solarlink-ar/solarlink-web/Documentación/Códigos/Carpeta Tecnica Solar Link/Fuentes.tex

\href{https://en.wikipedia.org/wiki/Maximum_power_point_tracking}{Seguidor de punto de maxima potencia, Wikipedia}\\

\href{https://en.wikipedia.org/wiki/Buck_converter}{Conversor buck, Wikipedia}\\

\href{https://es.wikipedia.org/wiki/Controlador_PID}{Controladores PID, Wikipedia}\\

\href{https://oa.upm.es/55985/1/TFG_ALBERTO_JIMENEZ_DE_LA_PENA.pdf}{Diseño de convertidor DC/DC con control reomoto para smartigrids}\\

\href{https://repositorio.uca.edu.ar/bitstream/123456789/11949/1/Bassani%20Mariano.%20TRABAJO%20FINAL%20DE%20MBA_MB_20210311_v2.pdf}{Trabajo final de Facultad de Ciencias Económicas de la UCA: ¿Es negocio invertir en generación eléctrica solar en Argentina?}\\

\href{https://www.un.org/es/chronicle/article/la-promesa-de-la-energia-solar-estrategia-energetica-para-reducir-las-emisiones-de-carbono-en-el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,ahorrar%20600%20kilogramos%20de%20CO2}{Organización de las Naciones Unidas: La promesa de la energía solar: Estrategia energética para reducir las emisiones de carbono en el siglo XXI}\\

\href{https://ri.conicet.gov.ar/handle/11336/182578?show=full}{Estado del arte de la tecnología de celdas solares basadas en semiconductores}\\

\href{https://docs.python.org/3/index.html}{Python 3.12.0 documentation}\\

\href{https://docs.djangoproject.com/en/4.2/}{Django documentation}\\

\href{https://docs.micropython.org/en/latest/}{MicroPython documentation}\\

\href{https://microdot.readthedocs.io/en/latest/}{Microdot documentation}\\

\href{https://github.com/solarlink-ar/solarlink}{Solar Link GitHub}\\

\href{https://solarlink.ar}{Web de Solar Link}\\
