solarlink-ar/solarlink-web/Documentación/Códigos/Presentación Proambiente Solar Link/resumen.tex

Solar Link es un administrador inteligente de energía eléctrica (Smart Grid) único en su tipo, que busca incentivar y maximizar el uso de energías renovables. A través de paneles solares, y con un sistema inteligente, alimentar todo el consumo hogareño posible con energía solar, “switcheando” las líneas de la casa (ejemplo iluminación, tomacorrientes) entre la línea eléctrica del proveedor (edesur o edenor p/ej) y la alimentación renovable.\\

La aplicación web, vinculada con el tablero del usuario, puede mostrar el consumo hogareño en tiempo real, cuánto se consumió de cada origen y se ahorró en el último tiempo, cuánto significa esto en términos de ahorro de dinero en la factura de luz, a modo de concientización en la importancia del uso de este tipo de energía.\\

En caso de cortes de suministro de luz, Solar Link puede encargarse de lo esencial de la casa que haga falta alimentar, siempre que esté en su margen de funcionamiento. \\

Por último, el proyecto plantea ser modular, versátil y económico, de forma tal que el tablero puede trabajar con cualquier cantidad de paneles o baterías que se le suministren: Solar Link no está limitado sólo a una fuente de energía solar. Aunque el enfoque de nuestro proyecto es aprovechar este tipo de energía, el sistema permite aprovechar también cualquier tipo de fuente: desde una red de proveedor extra, pasando por cosas como un grupo electrógeno, y hasta otras fuentes renovables; biogas, eólica, entre otras. \\
