solarlink-ar/solarlink-web/Documentación/Presentación_Proambiente_Solar_Link.pdf

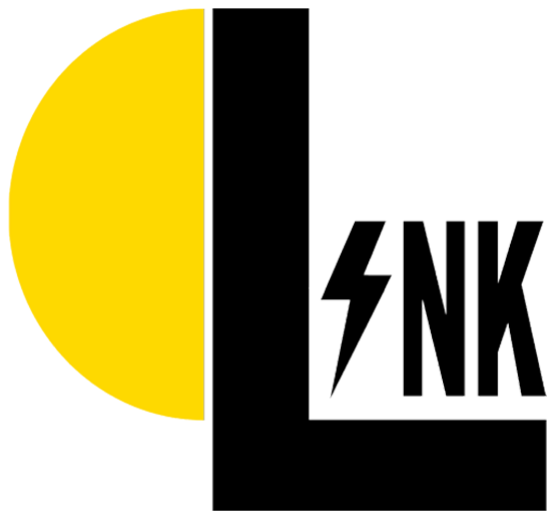
[picture p185: figure]

# Solar Link Propuesta ambiental de futuro sostenible

## Cenyko, Ivan Ezequiel Dias, Lara Paloma Inza Fior, Mateo Palmieri Hise, Agustín Testa, Maximiliano Nicolas

2023

## Índice

1. Preámbulo | 2
2. Resumen del proyecto | 6
3. Desarrollo del proyecto | 6
4. Impacto ambiental | 8
5. Beneficios sociales | 11
6. Conclusiones | 14
7. Anexo | 15

1

## 1. Preámbulo

1.1. ¿Quiénes somos?

Ivan Ezequiel Cenyko


DNI: 46.028.174

Mail: ivancenyko@gmail.com

Linkedin: www.linkedin.com/in/ivan-cenyko/

Programación en microPython y desarrollo web Back-End

Lara Paloma Dias


DNI: 46200006

Mail: palomadias308@gmail.com

Linkedin: www.linkedin.com/in/lara-paloma-dias-598bb9288/

Desarrollo web Front-End

2

Mateo Inza Fior


DNI: 46.579.589

Mail: mateoinzafior@gmail.com

Linkedin: www.linkedin.com/in/mateoinzafior/

Desarrollo web Front-End y programación en microPython

Agustin Palmieri Hise


DNI: 46.364.013

Mail: aguspalmierihise@gmail.com

Linkedin: www.linkedin.com/in/agustin-palmieri-hise/

Diseño y confección eléctrico y electrónico íntegro


Maximiliano Nicolas Testa

DNI: 46.187.213

Mail: maxitesta2012@gmail.com

Linkedin: www.linkedin.com/in/maximiliano-testa/

Programación en C y desarrollo Front-End de la Web-app

3


Figura 1: Equipo Solar Link

### 1.2. Contacto

Podes encontrar a Solar Link en:

Mail: info@solarlink.ar

Pagina Web: www.solarlink.ar

Instagram: www.instagram.com/solarlink.ar/

Github: github.com/solarlink-ar/solarlink

Trello: trello.com/w/2023_721c_solarlink

### 1.3. Docentes a cargo

Sergio Medina
Nos fue de ayuda a la hora de organizar y presentar nuestro proyecto.

4

Fabrizio Carlassara
Nos guió en el desarrollo de todo el software del proyecto.

Diego Palmieri
Nos prestó las herramientas y los medios necesarios para confeccionar el proyecto.

### 1.4. Agradecimientos

Este proyecto no hubiera sido posible sin la colaboracion de los docentes anteriormente mencionados, la Asociación Cooperadora IMPA y las empresas Roverano, Exo y Newton Microscopios.

5

## 2. Resumen del proyecto

Solar Link es un administrador inteligente de energía eléctrica (Smart Grid) único en su tipo, que busca incentivar y maximizar el uso de energías renovables. A través de paneles solares, y con un sistema inteligente, alimentar todo el consumo hogareño posible con energía solar, “switcheando” las líneas de la casa (ejemplo iluminación, tomacorrientes) entre la línea eléctrica del proveedor (edesur o edenor p/ej) y la alimentación renovable.

La aplicación web, vinculada con el tablero del usuario, puede mostrar el consumo hogareño en tiempo real, cuánto se consumió de cada origen y se ahorró en el último tiempo, cuánto significa esto en términos de ahorro de dinero en la factura de luz, a modo de concientización en la importancia del uso de este tipo de energía.

En caso de cortes de suministro de luz, Solar Link puede encargarse de lo esencial de la casa que haga falta alimentar, siempre que esté en su margen de funcionamiento.

Por último, el proyecto plantea ser modular, versátil y económico, de forma tal que el tablero puede trabajar con cualquier cantidad de paneles o baterías que se le suministren: Solar Link no está limitado sólo a una fuente de energía solar. Aunque el enfoque de nuestro proyecto es aprovechar este tipo de energía, el sistema permite aprovechar también cualquier tipo de fuente: desde una red de proveedor extra, pasando por cosas como un grupo electrógeno, y hasta otras fuentes renovables; biogas, eólica, entre otras.

## 3. Desarrollo del proyecto

Nuestra propuesta para solventar algunas desventajas de los sistemas de energía renovable (especialmente la solar) es crear un sistema autónomo e inteligente que, a través de un sistema off-grid, sea capaz de acoplar y desacoplar la casa de la red eléctrica convencional, dependiendo del consumo de la misma.

Este sistema debe ser capaz de leer el consumo de las líneas de la casa, y debe conocer la potencia que el sistema solar instalado puede entregar. De esta manera, cuando se detecte que el consumo de la casa puede ser alimentado por el sistema off-grid, dejará de alimentar la casa con el proveedor

6

de energía eléctrica. Mientras que si el consumo supera el límite establecido, volverá a alimentarla. Para realizar esto, se utiliza la técnica “cruce por cero”, para sincronizar el cambio entre líneas, y que no se note este cambio.

Puede ocurrir que en una casa estén constantemente heladeras, calefactores, computadoras, y otros electrodomésticos de alto consumo en uso, y que el sistema off-grid nunca pueda ser capaz de alimentar la línea general de la casa. Para esto, proponemos que Solar Link trabaje parcialmente sobre la casa, pudiendo alimentar independientemente la línea de iluminación y la línea de tomas de la casa. Es decir, si se da el caso mencionado anteriormente, la línea de iluminación seguiría siendo alimentada por energía solar, mientras que la línea de tomas la sería alimentada por el proveedor de energía eléctrica.

En caso de un corte de suministro de luz,el sistema Solar Link seguiría funcionando, alimentando a la mayor parte de la casa posible.
Un aspecto clave del proyecto es la accesibilidad e interacción con el usuario. Solar Link incluye una aplicación vinculada con sensores distribuidos en la red eléctrica de la casa. El usuario podrá así tener una noción más concreta de cuáles son los principales consumos del hogar, y le brinda la información necesaria a Solar Link para alternar el uso de energía off-grid y energía de red en cada línea modular.

Además, para optimizar la carga del sistema solar, desarrollamos un cargador MPPT de 3 etapas que no solo le da la mejor carga posible a las baterías del sistema, sino que también monitorea el estado de carga de las mismas, y se lo comunica al módulo Solar Link para tenerlo en cuenta a la hora de la conmutación entre lineas, y a la hora de entregarle la mayor cantidad de información posible sobre el sistema al usuario.

7

## 4. Impacto ambiental

### 4.1. El aspecto de energías no renovables

Las principales fuentes de energía con las que cuenta hoy el mundo, petróleo, gas natural y carbón mineral, son de carácter no renovable o convencional; es decir que a medida que se van consumiendo disminuyen sus reservas sin posible reposición, salvo que se descubran nuevos yacimientos.

Este sector de energías convencionales sigue teniendo un papel protagónico en la matriz energética mundial, producto de un mercado con muchos años de desarrollo tecnológico, con un gran capital hundido en infraestructura, costos competitivos y con porcentajes de rendimiento y de potencia firme superiores a las renovables. Sin embargo, el consumo de combustibles de origen fósil tiene un efecto muy negativo para el medio ambiente, ya que el dióxido de carbono que se produce por su combustión es el principal constituyente de lo que se conoce como gases de efecto invernadero, principales responsables del calentamiento global.

Las consecuencias de este efecto son, por ejemplo, el aumento de las temperaturas, los picos de temperaturas extremos, que han venido manifestándose en los últimos años. Es por ello, que las emisiones globales de carbono continúan aumentando, lo que indica la necesidad de un conjunto integral de medidas políticas para lograr la reducción sustancial de las emisiones de carbono.

8


Figura 2: Matriz de generación energética en Argentina

En Argentina, casi el 60 % de la energía producida y distribuida en el país son de carácter no renovable. La visión de Solar Link es aportar a que ésta brecha vaya disminuyendo hasta su exterminacion, volviendo a las energias renovables cabecillas en la generacion de energia.

### 4.2. Uso de baterías en la actualidad

En la actualidad, las baterías de litio están tomando cada vez mas protagonismo en el mercado. Estas, luego de su uso, se vuelven obsoletas y generan desechos que no son reciclables, sin contar que su extracción es altamente nociva y genera residuos contaminantes.

La solución que nosotros proponemos es impulsar el uso de baterías de plomo ácido, que no solo son reciclables hasta en un 80 %, sino que tienen una expectativa de vida mayor. Esto sumado al cargador MPPT de Solar Link, que maximiza el potencial recibido de una fuente de energía renovable y la vida útil de las baterías, creemos que es una solución tanto viable como económica.

9

### 4.3. El aspecto de la energía solar

El sol es el mayor suministro de energía que dispone la humanidad disponible de forma ilimitada y que puede ser aprovechada en cualquier parte del mundo. Existen dos maneras principales de capturar esta energía solar: la fotovoltaica y la térmica, ambas comparten la virtud que pueden ser producidas y consumidas en cualquier lugar, tanto en áreas remotas o grandes ciudades.

En las economías emergentes, como la Argentina, donde existe déficit de infraestructura en generación, transporte y distribución, esta energía permite soluciones de generación a los individuos o poblaciones aisladas.

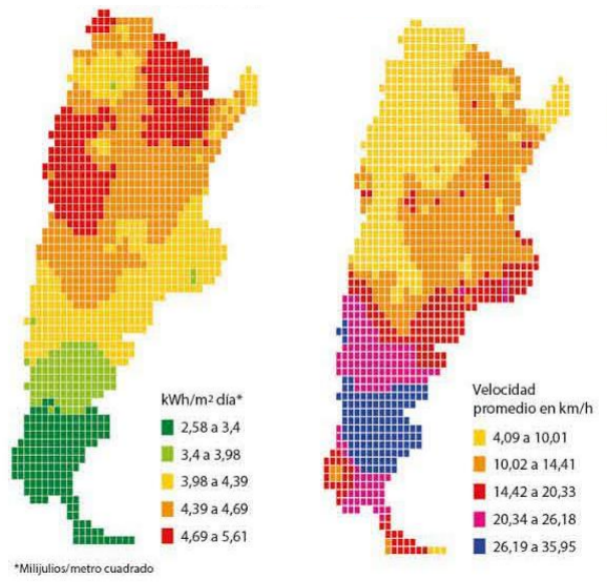
[picture p186: figure]

(a) Zonas del pais con mayor promedio de intensidad de
radiación solar
(b) Zonas del pais con mayor promedio de intensidad de
los vientos

Nótese que justamente las provincias con más potencial solar (inclusive eólico) son aquellas donde el consumo de energía eléctrica es mucho más caro en comparación con el gran Bs As y otros centros urbanos, principalmente por los altos costos de distribución de energía. Acá es donde Solar

10

Link tendría su mayor aprovechamiento.

Considerando la estadística mostrada, un metro cuadrado de panel solar (en bs as) podría generar 4 kW/h por día. Suponiendo que el panel está en uso 12hs por día, se generan 330 W/h por metro cuadrado de panel. En realidad, los paneles son menos eficientes que esto, por tanto para recibir esos 330W/h los paneles son más grandes que 1 metro cuadrado.
Sabiendo esto, usaremos como ejemplo un panel solar de 380 W/h y 1.75 metros cuadrados. Por tanto durante, en promedio, 12 hs, se recibirán 380 W/h en el panel. Esta generación de energía implica que por día se producen 4.56 kW/h.

En promedio, por mes, una casa de núcleo familiar consume 600 kW/h, o sea 20 kW/h por día. Si hacemos números, nos da que el sistema sería capaz de alimentar con energía solar el 25 % de esa carga (en promedio), ya que de los 600 kW/h por mes, 140 pudieron generarse con el sistema para cargar las baterías y que estas después alimenten las líneas competentes.

Hoy en dia el desarrollo de la tecnologia relacionado con la energía solar crece exponencialmente, haciendo mas barato y accesible estos sistemas. A su vez, en argentina disminuye el subsidio destinado a la distribución eléctrica, cerrando lentamente la brecha monetaria entre pagar la luz y recurrir a energias renovables.

Teniendo en cuenta todo lo dicho anteriormente, el uso de energias renovables no solo se esta volviendo plausible, sino que tambien se esta volviendo rentable y accesible. Nuestro objetivo con Solar Link es volver esta esperanza en una realidad.

## 5. Beneficios sociales

### 5.1. Beneficio económico

Solar Link propone el uso de un sistema solar off-grid de baja potencia, el cual es la alternativa mas económica que se consigue de energía solar. Este sistema consta de panel/es solar/es, batería/s, nuestro cargador MPPT de 3 etapas y un inverter.

El sistema que recomendamos instalar en un hogar promedio en Argentina, se compone de dos paneles solares de 380W, un inverter de 2000W,

11 dos baterías de ciclo profundo de 110Ah, el cargador MPPT de 3 etapas de Solar Link, y el módulo Solar Link, con un costo total aproximado de esto ARS $1.600.000 (USD $1.600).

Mientras tanto, un sistema comparable on-grid, puede salir ARS $5.000.000 (USD $5.000). Esto depende del servicio que se contrate y de la empresa que lo realice.

No está de más mencionar que al uno producir la energía que consume, se disminuye el consumo de energía de terceros, el del proveedor eléctrico. Esto quiere decir, que todos los meses se verá reducido el precio que hay que pagar por el suministro de energía eléctrico.

El ahorro en este caso no es lineal. Si uno termina consumiendo a fin de mes la mitad de energía que consumiría normalmente, por como funciona el sistema de cobros de las empresas distribuidoras en Argentina, no pagaría la mitad, sino que bastante menos.

Esto ocurre porque las empresas establecen un precio para cada KW/h dependiendo de la escala en donde se consuma. Por ejemplo, entre 0KW/h y 200KW/h tiene un precio asignado, entre 200KW/h y 400KW/h otro mayor, y si se exceden esos 400KW/h otro inclusive mayor (estas escalas dependen de la empresa a cargo del suministro eléctrico).

Osea, digamos, que cada KW/h entre 0KW/h y 200KW/h valga 1, entre 200KW/h y 400KW/h, 1,5, y si es mayor a 400KW/h, 2. si uno consume 600KW/h, estaría pagando 900, mientras que si uno consume 300KW/h, estaría pagando 350, bastante menos de la mitad. Este ejemplo ilustra como funciona el sistema de cobros de las compañías distribuidoras en Argentina. Las escalas y los valores son a modo de ejemplo. Pueden ser diferentes segun la empresa, la región, y el momento en donde se analice.

### 5.2. Incentivo y concientización

A través de nuestra aplicación, el usuario tendrá acceso a toda la información que respecta al consumo eléctrico de su casa. Esto le permite conocer al detalle no solo el consumo total, sino tambien el consumo que generó el sistema solar propio.

Esto genera en el usuario un sentido de ganancia y de gasto propio. Saber

12 bien cuanto se esta gastando, porque y cuanto de este gasto se amortiguo ayuda a concientizar sobre el consumo de energia en general.

Mas allá del gasto de energía, tener un sistema que, ya sea de manera directa o indirecta, ayuda al medio ambiente, tiene un efecto positivo para la psiquis y para el entorno donde uno vive. Saber que uno esta aportando su grano de arena (siendo el mismo economicamente viable y rentable) genera tranquilidad y un sentido de responsabilidad ciudadana.

### 5.3. Estado del arte

Actualmente, en el mercado argentino, existen principalmente tres tipos de instalaciones de energía solar para un hogar. Cada tipo cuenta con sus propias ventajas y desventajas:

Tipo | Ventajas | Desventajas
On-Grid | Sistema acoplado a la línea doméstica Alimenta casi el 100 % con energía solar | Alto costo Desperdicio de energía
Off-Grid | Económico Acumula energía | Requiere una línea exclusiva para este sistema
Híbrido | Sistema acoplado a la línea doméstica Acumula energía | Potencia limitada Requiere instalación especial

Los sistemas on-grid, como su nombre lo indica, se instalan directamente
en la línea de la casa. Toda la energía que producen los paneles se entregan a la línea general de la casa, sin almacenarse en ningún lado. Si la casa consume mas que lo que generan los paneles, se consume la energía correspondiente a este exceso del proveedor eléctrico, y si consume menos, la energía generada por demás se entrega a la red eléctrica del proveedor.

Para este tipo de sistemas es necesaria la instalación de un medidor bidireccional, que mide tanto el consumo de la casa como lo que devuelve por el exceso en la producción. Si bien este medidor descuenta lo que uno devuelve a la red eléctrica, lo que uno consume es mas caro, no es muy redituable y no su instalación depende del proveedor de energía eléctrica.

Los sistemas off-grid, por otra parte, acumulan la energía generada por los paneles solares en baterías, para luego convertirla en los 220Vac que necesita la casa. El problema de esto, es que la energía extraída de las baterías no se puede incorporar directamente a la línea de la casa, por lo que

13 es necesario la utilización de una línea exclusiva para lo que este sistema genere. Esto implica tener que hacer una instalación eléctrica aislada e independiente del resto de la casa, algo impráctico si además se tiene en cuenta que la utilización de esta línea debe ser controlada y depende directamente de la carga de los paneles.

Los sistemas híbridos son sistemas solares off-grid que se incorporan a la línea de la casa. Pueden utilizar tanto la energía solar acumulada como la energía del proveedor eléctrico. Para utilizar este tipo de sistema es necesaria una instalación especial, que se tiene que realizar en líneas dedicadas. Además, por como es su principio de funcionamiento, el sistema solar no es expandible, por lo que la potencia instalada en un principio no podrá modificarse.

Mientras tanto, Solar Link busca recopilar todas las ventajas de estos 3 tipos de sistemas solares, y dejar en el camino todas las desventajas posibles. Se podría decir que Solar Link es un sistema que acumula y utiliza energía solar, acoplado a la línea de la casa, económico, modular expandible y amigable con el usuario, compartiendo toda la información necesaria sobre el sistema solar instalado y el consumo de la casa.

## 6. Conclusiones

Solar Link aprovecha sus cualidades como gestor inteligente para poder aprovechar la energía solar al máximo. Usualmente, la instalación de una fuente de energía solar por sí sóla no daría abasto para toda la casa (recordemos que en nuestro ejemplo sólo cubría el 30 %), y otros tipos de implementación alternativas a una red inteligente serían rígidas e ineficientes. A través de Solar Link, buscamos que con el control automático de consumo y la separación modular de las redes de la casa logremos maximizar la eficiencia en el consumo, y minimizar los gastos posibles.

Nuestro objetivo es introducir al país un sistema capaz de evitar energía cuya generación es, en su mayoría, resultado de fomentar el cambio climático, introduciendo energías renovables y control y concientización del consumo a sus usuarios, en otras palabras un smart grid con energías renovables. Por otro lado, otorga a sus usuarios energía generada por ellos mismos para su hogar, y por lo tanto, no deben pagar por ella.

Entre sus beneficios están, el uso de energías renovables, la producción de energía en el propio entorno de uso, que reduciría el consumo en la boleta,

14 una aplicación web que permite ver el consumo y configurarlo, dando control al usuario de su consumo y que sea consciente de este.

## 7. Anexo

### 7.1. Referencias

Trabajo final de Facultad de Ciencias Económicas de la UCA: ¿Es negocio invertir en generación eléctrica solar en Argentina? (https://repositorio.uca.edu.ar/bitstream/123456789/11949/1/Bassani%20Mariano.%20TRABAJO%20FINAL%20DE%20MBA_MB_20210311_v2.pdf)

Organización de las Naciones Unidas: La promesa de la energía solar: Estrategia energética para reducir las emisiones de carbono en el siglo XXI (https://www.un.org/es/chronicle/article/la-promesa-de-la-energia-solar-estrategia-energetica-para-reducir-las-emisiones-de-carbono-en-el)

Estado del arte de la tecnología de celdas solares basadas en semiconductores (https://ri.conicet.gov.ar/handle/11336/182578?show=full)

15
