solarlink-ar/solarlink-web/Documentación/Códigos/Carpeta de campo/informes/876842E6-08C9-4F52-9927-B1110389220B.jpg

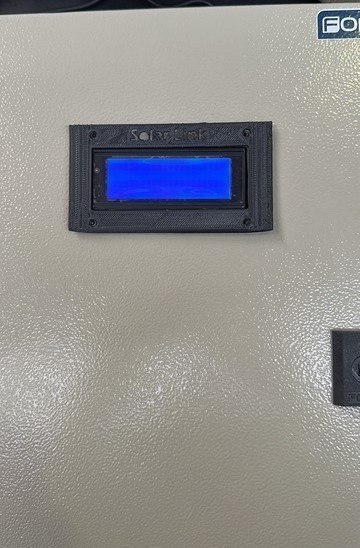
Documentación/Códigos/Carpeta de campo/informes/876842E6-08C9-4F52-9927-B1110389220B.jpg
