solarlink-ar/solarlink-web/Documentación/Códigos/Carpeta de campo/informes/E2ECCB4C-C0EE-4EAA-B4AB-5EC7912F2BAF.jpg

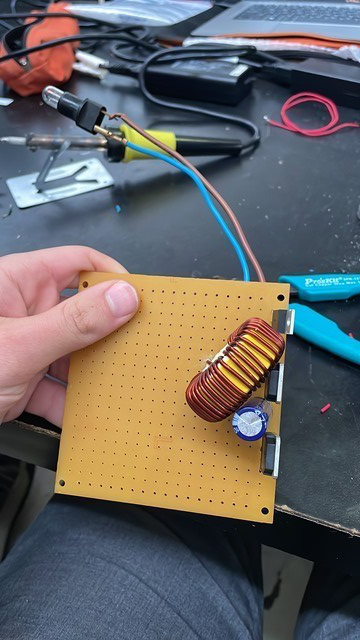
Documentación/Códigos/Carpeta de campo/informes/E2ECCB4C-C0EE-4EAA-B4AB-5EC7912F2BAF.jpg
