solarlink-ar/solarlink-web/Documentación/Códigos/Carpeta de campo/informes/IMG_8020.jpg

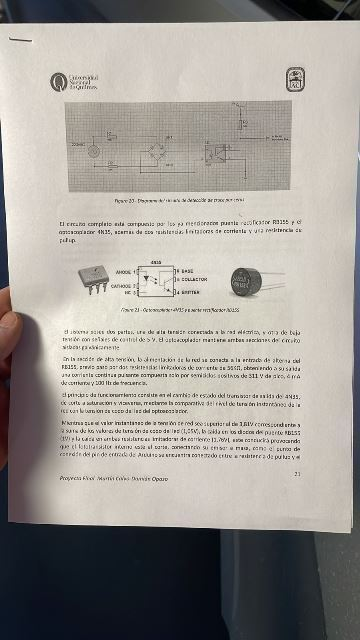
Documentación/Códigos/Carpeta de campo/informes/IMG_8020.jpg
