solarlink-ar/solarlink-web/Documentación/Códigos/Carpeta de campo/informes/IMG_8021.jpg

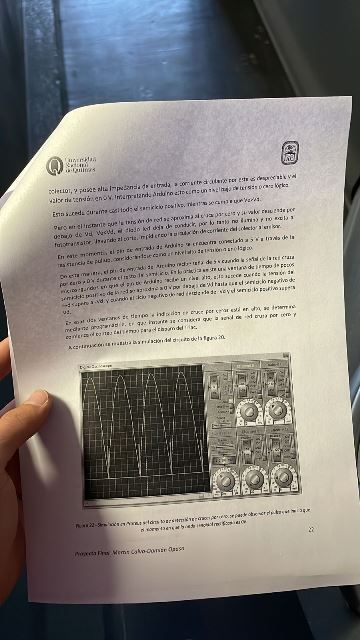
Documentación/Códigos/Carpeta de campo/informes/IMG_8021.jpg
