solarlink-ar/solarlink-web/Documentación/Códigos/Carpeta de campo/informes/IMG_8863.jpg

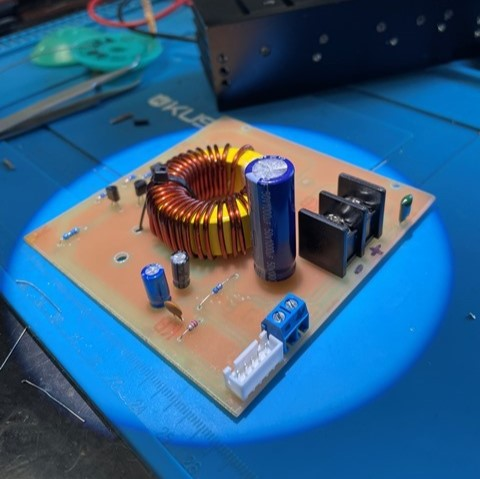
Documentación/Códigos/Carpeta de campo/informes/IMG_8863.jpg
