solarlink-ar/solarlink-web/Documentación/Códigos/Carpeta de campo/informes/IMG_9290.jpg

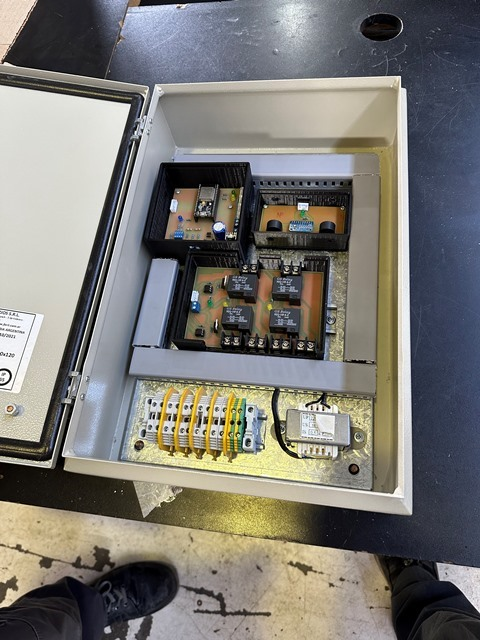
Documentación/Códigos/Carpeta de campo/informes/IMG_9290.jpg
