solarlink-ar/solarlink-web/Documentación/Códigos/Carpeta de campo/informes/IMG_9307.jpg

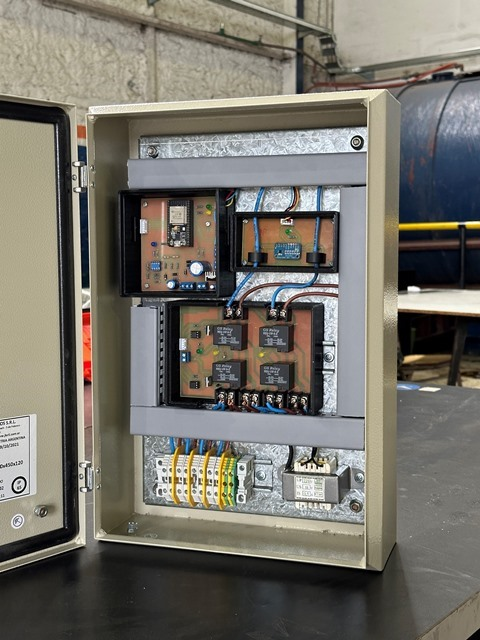
Documentación/Códigos/Carpeta de campo/informes/IMG_9307.jpg
