solarlink-ar/solarlink-web/Documentación/Códigos/Carpeta de campo/informes/Screenshot_5.jpg

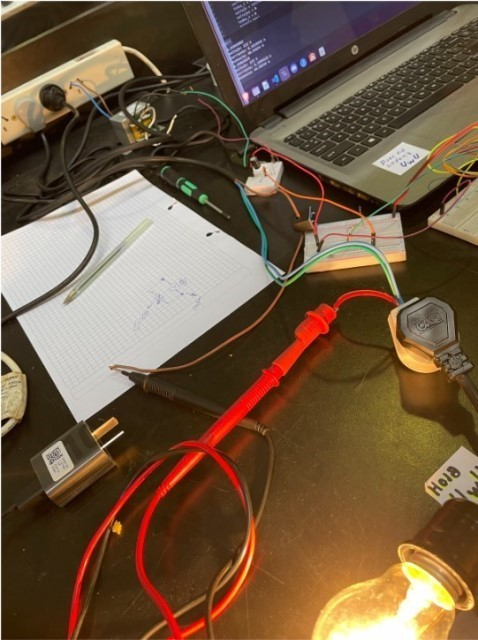
Documentación/Códigos/Carpeta de campo/informes/Screenshot_5.jpg
