solarlink-ar/solarlink-web/Documentación/Códigos/Carpeta de campo/informes/Screenshot_9.jpg

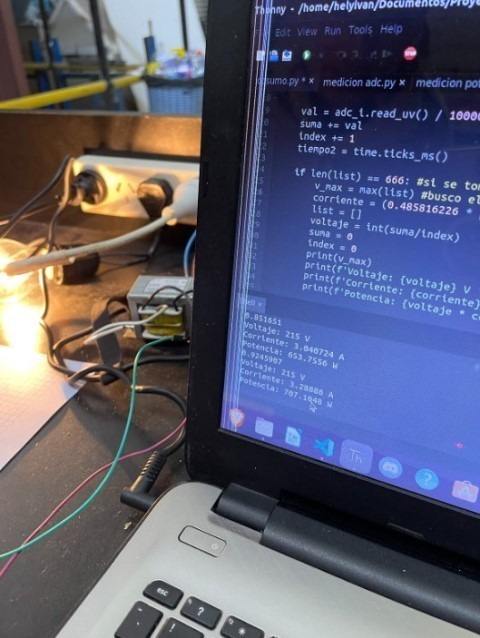
Documentación/Códigos/Carpeta de campo/informes/Screenshot_9.jpg
