solarlink-ar/solarlink-web/Documentación/Códigos/Carpeta Tecnica Solar Link/analisis-tecnico/Diagrama aplicacion SolarLink.png

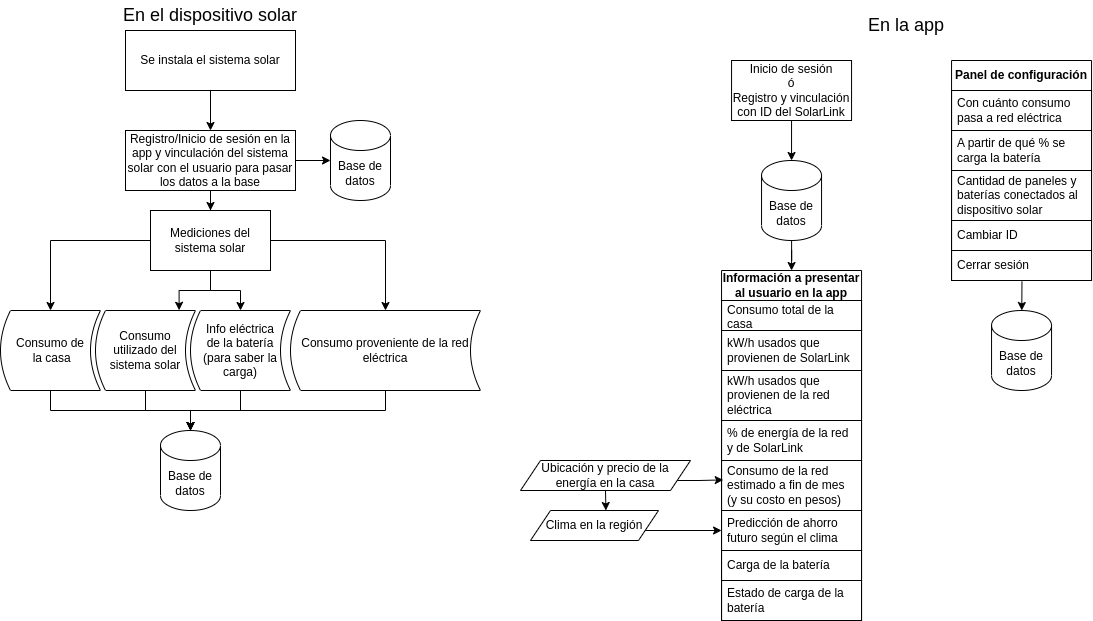
Documentación/Códigos/Carpeta Tecnica Solar Link/analisis-tecnico/Diagrama aplicacion SolarLink.png
