solarlink-ar/solarlink-web/Documentación/Códigos/Carpeta Tecnica Solar Link/hardware/IMG_8938.jpg

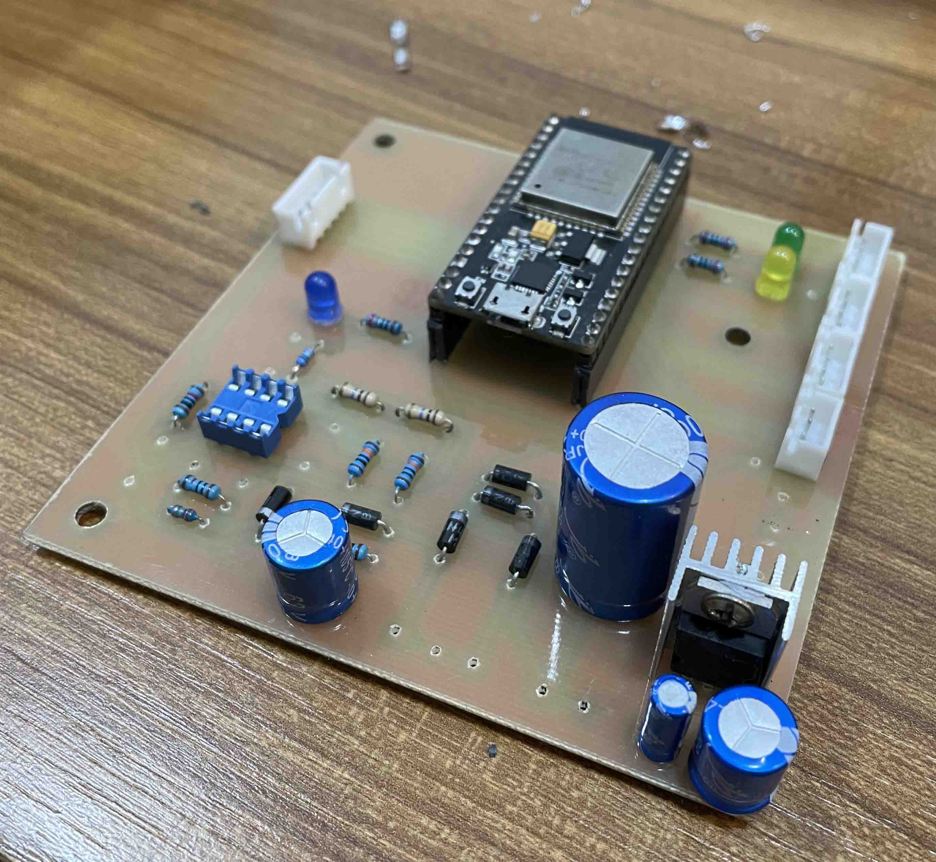
Documentación/Códigos/Carpeta Tecnica Solar Link/hardware/IMG_8938.jpg
