solarlink-ar/solarlink-web/Documentación/Códigos/Carpeta Tecnica Solar Link/hardware/mosfet.jpg

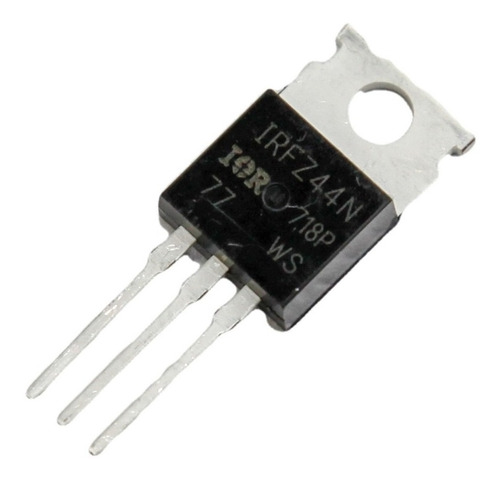
Documentación/Códigos/Carpeta Tecnica Solar Link/hardware/mosfet.jpg
