solarlink-ar/solarlink-web/Documentación/Códigos/Carpeta Tecnica Solar Link/hardware/Screenshot_13.jpg

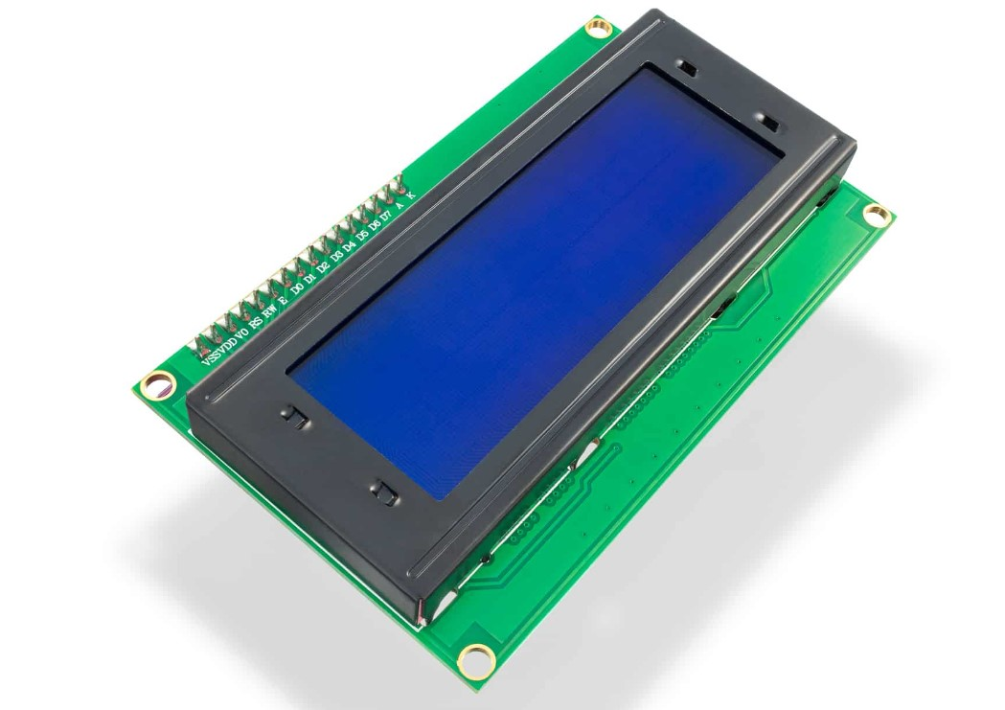
Documentación/Códigos/Carpeta Tecnica Solar Link/hardware/Screenshot_13.jpg
