solarlink-ar/solarlink-web/Documentación/Códigos/Carpeta Tecnica Solar Link/Intro/Screenshot_4.png

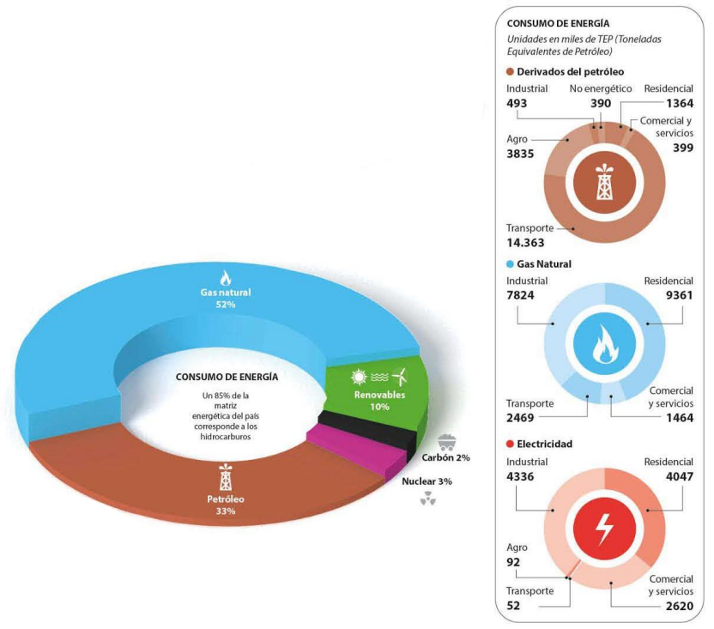
Documentación/Códigos/Carpeta Tecnica Solar Link/Intro/Screenshot_4.png
