solarlink-ar/solarlink-web/Documentación/Códigos/Carpeta Tecnica Solar Link/Intro/smart-grid.png

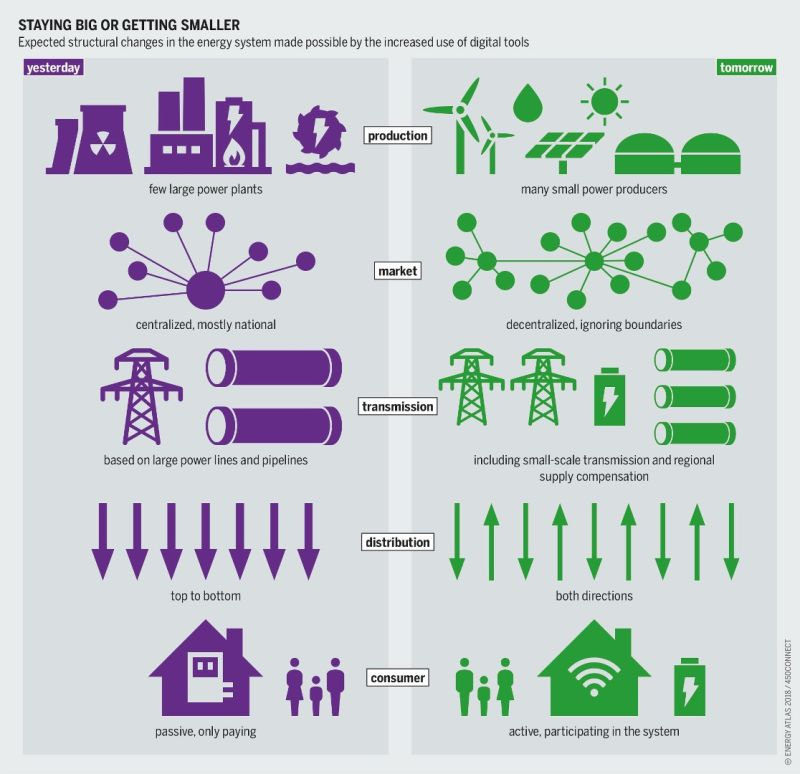
Documentación/Códigos/Carpeta Tecnica Solar Link/Intro/smart-grid.png
