solarlink-ar/solarlink-web/Documentación/Códigos/Carpeta Tecnica Solar Link/MPPT/800px-IUoU_charging_graph.png

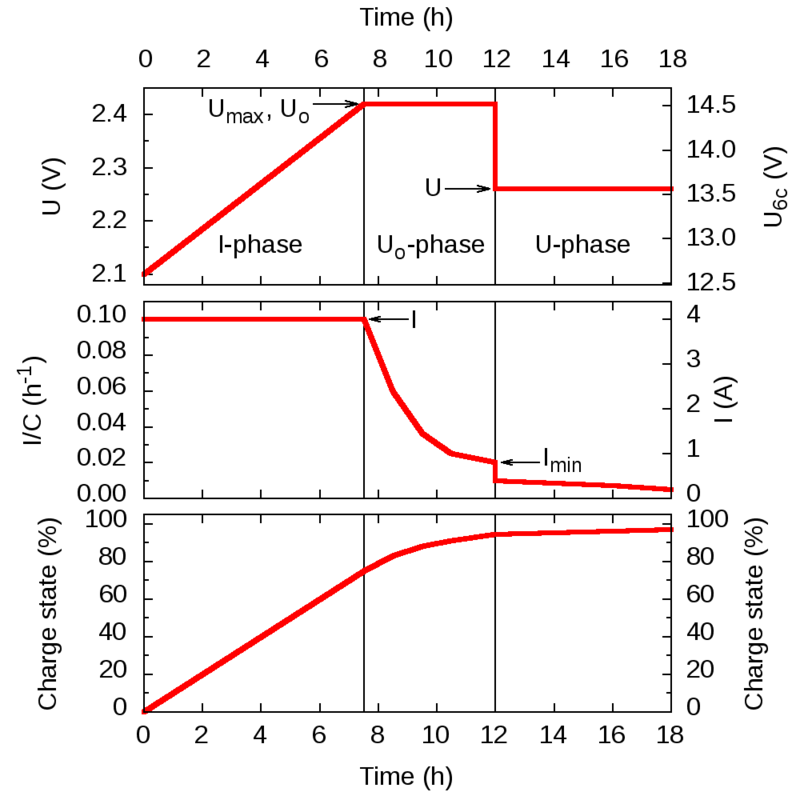
Documentación/Códigos/Carpeta Tecnica Solar Link/MPPT/800px-IUoU_charging_graph.png
