solarlink-ar/solarlink-web/Documentación/Códigos/Carpeta Tecnica Solar Link/MPPT/Screenshot_5.png

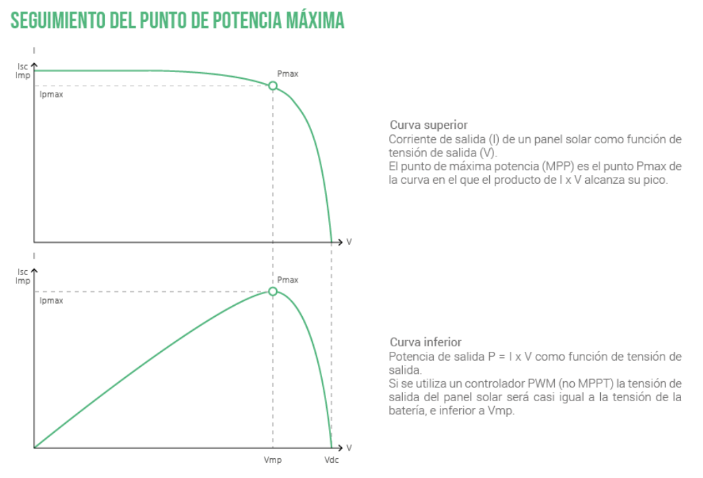
Documentación/Códigos/Carpeta Tecnica Solar Link/MPPT/Screenshot_5.png
