solarlink-ar/solarlink-web/Documentación/Códigos/Carpeta Tecnica Solar Link/MPPT/Screenshot_6.png

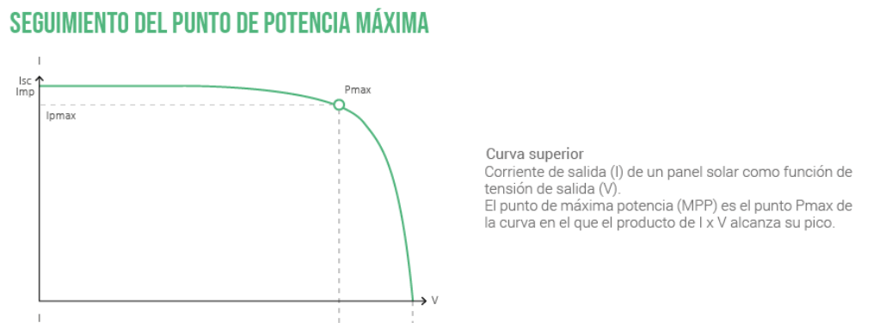
Documentación/Códigos/Carpeta Tecnica Solar Link/MPPT/Screenshot_6.png
