solarlink-ar/solarlink-web/Documentación/Códigos/Carpeta Tecnica Solar Link/preambulo/Captura de pantalla (18).png

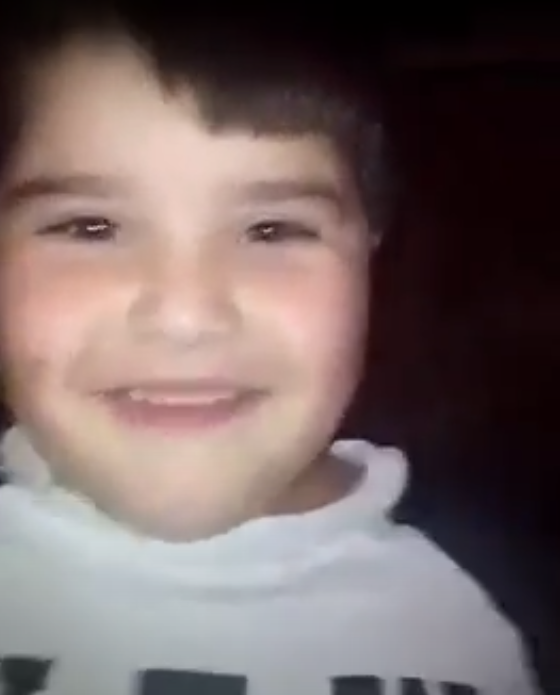
Documentación/Códigos/Carpeta Tecnica Solar Link/preambulo/Captura de pantalla (18).png
