solarlink-ar/solarlink-web/Documentación/Códigos/Carpeta Tecnica Solar Link/proto-final/IMG_7874.jpg

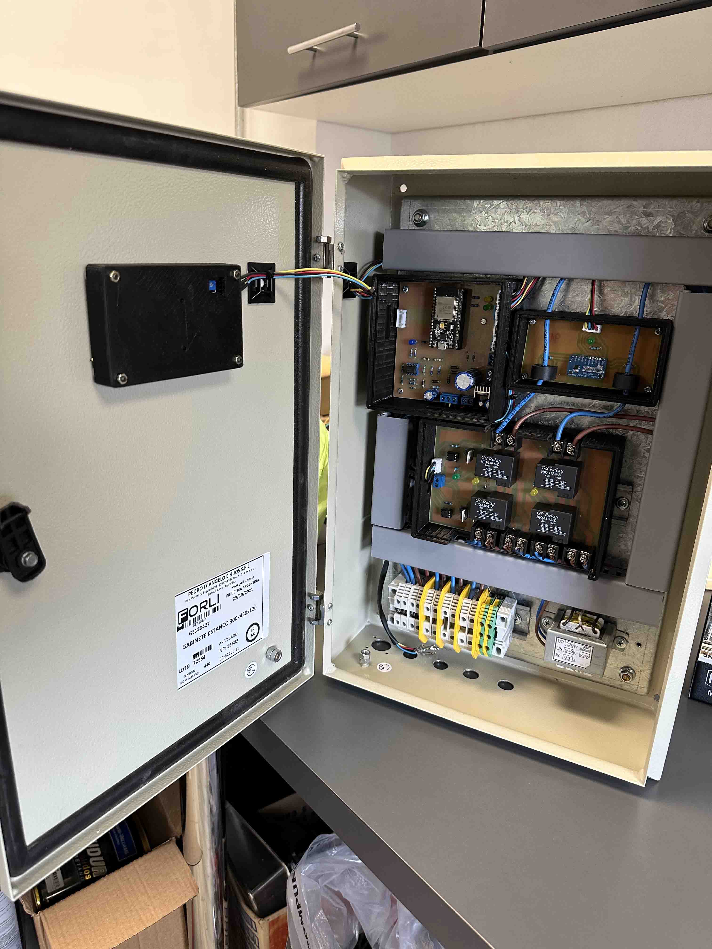
Documentación/Códigos/Carpeta Tecnica Solar Link/proto-final/IMG_7874.jpg
