solarlink-ar/solarlink-web/Documentación/Códigos/Carpeta Tecnica Solar Link/web/Captura desde 2023-10-15 23-22-38.png

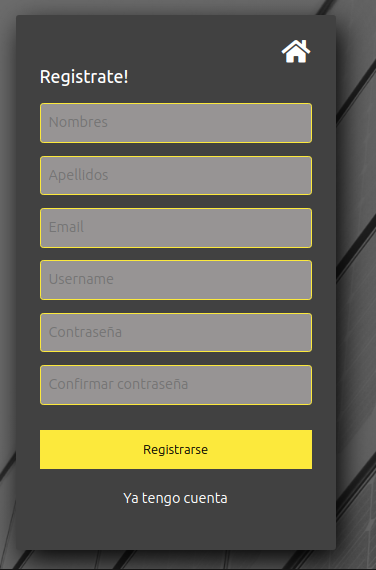
Documentación/Códigos/Carpeta Tecnica Solar Link/web/Captura desde 2023-10-15 23-22-38.png
