solarlink-ar/solarlink-web/PCBs/Conmutación/Screenshot_1.png

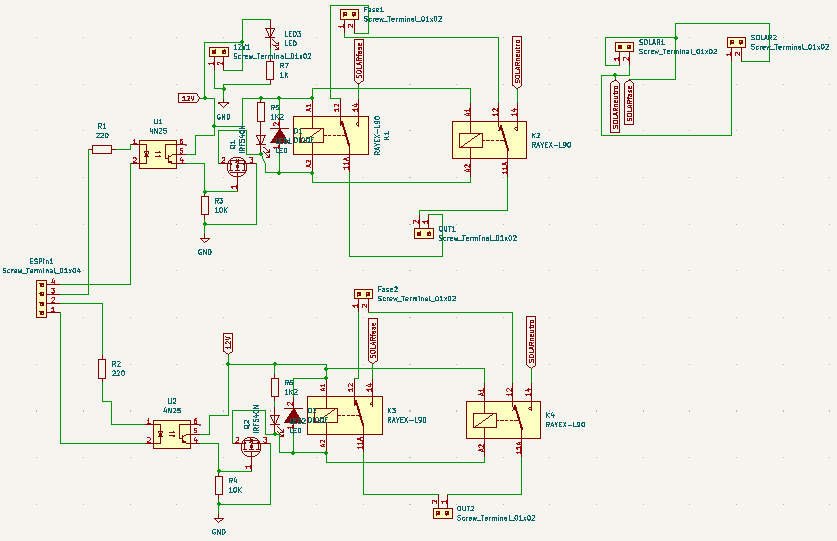
PCBs/Conmutación/Screenshot_1.png
