solarlink-ar/solarlink-web/PCBs/Conmutación/Screenshot_315.png

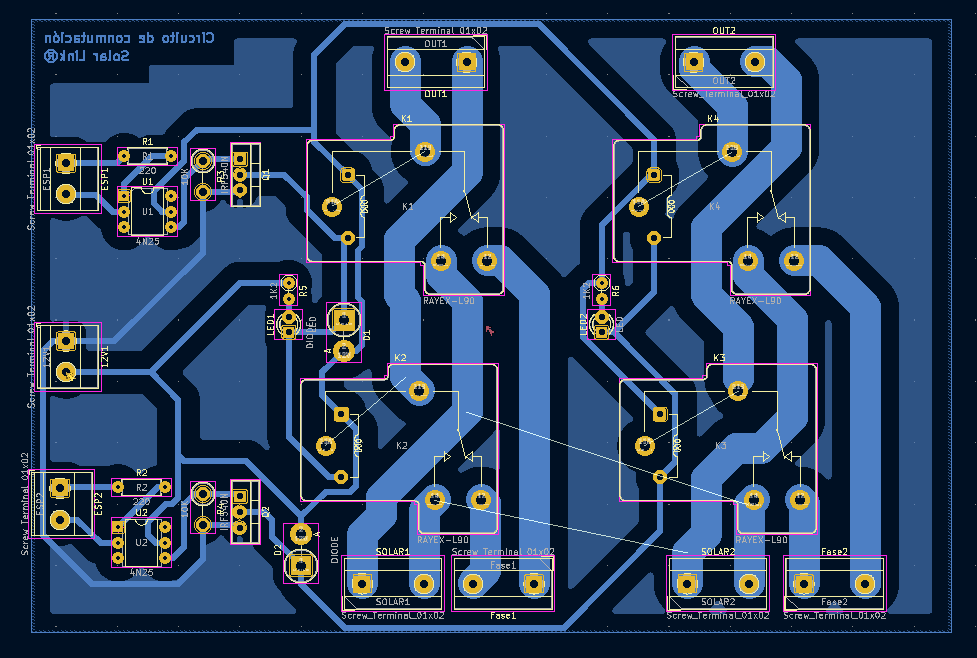
PCBs/Conmutación/Screenshot_315.png
