solarlink-ar/solarlink-web/PCBs/Conmutación/Screenshot_316.png

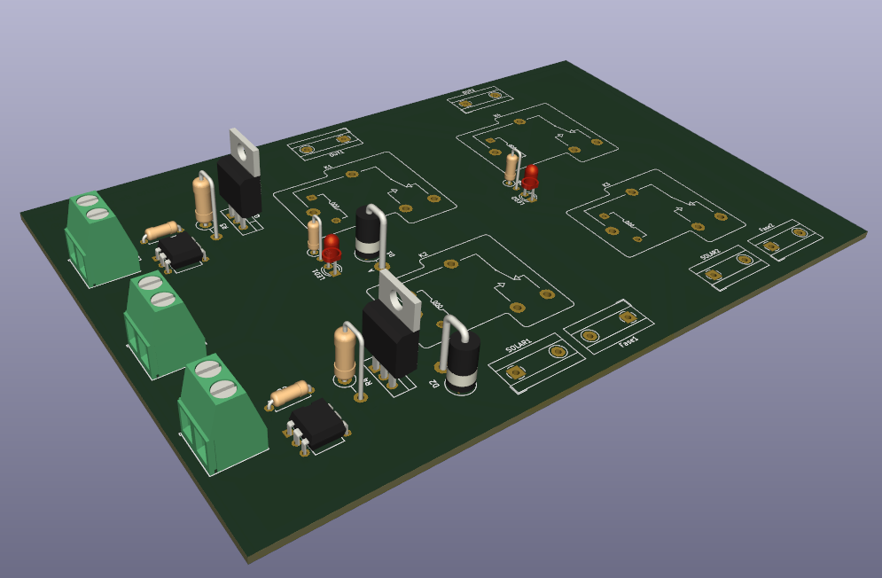
PCBs/Conmutación/Screenshot_316.png
