solarlink-ar/solarlink-web/PCBs/Conmutación/Screenshot_318-removebg-preview.png

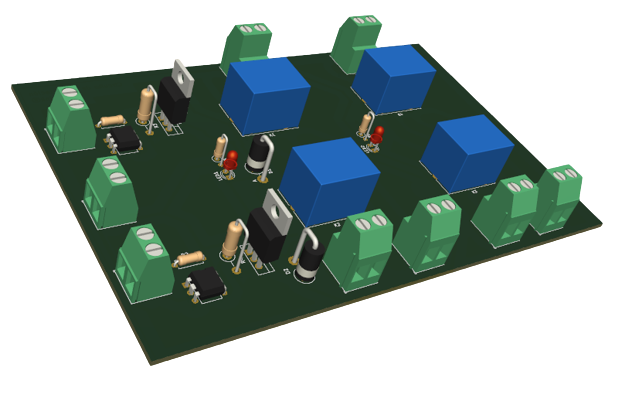
PCBs/Conmutación/Screenshot_318-removebg-preview.png
