solarlink-ar/solarlink-web/PCBs/Conmutación/Screenshot_318.png

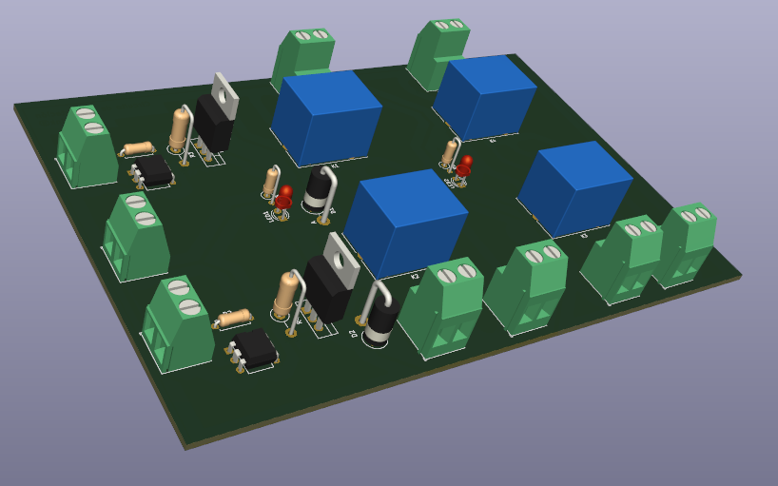
PCBs/Conmutación/Screenshot_318.png
