solarlink-ar/solarlink-web/PCBs/Conmutación/Screenshot_319.png

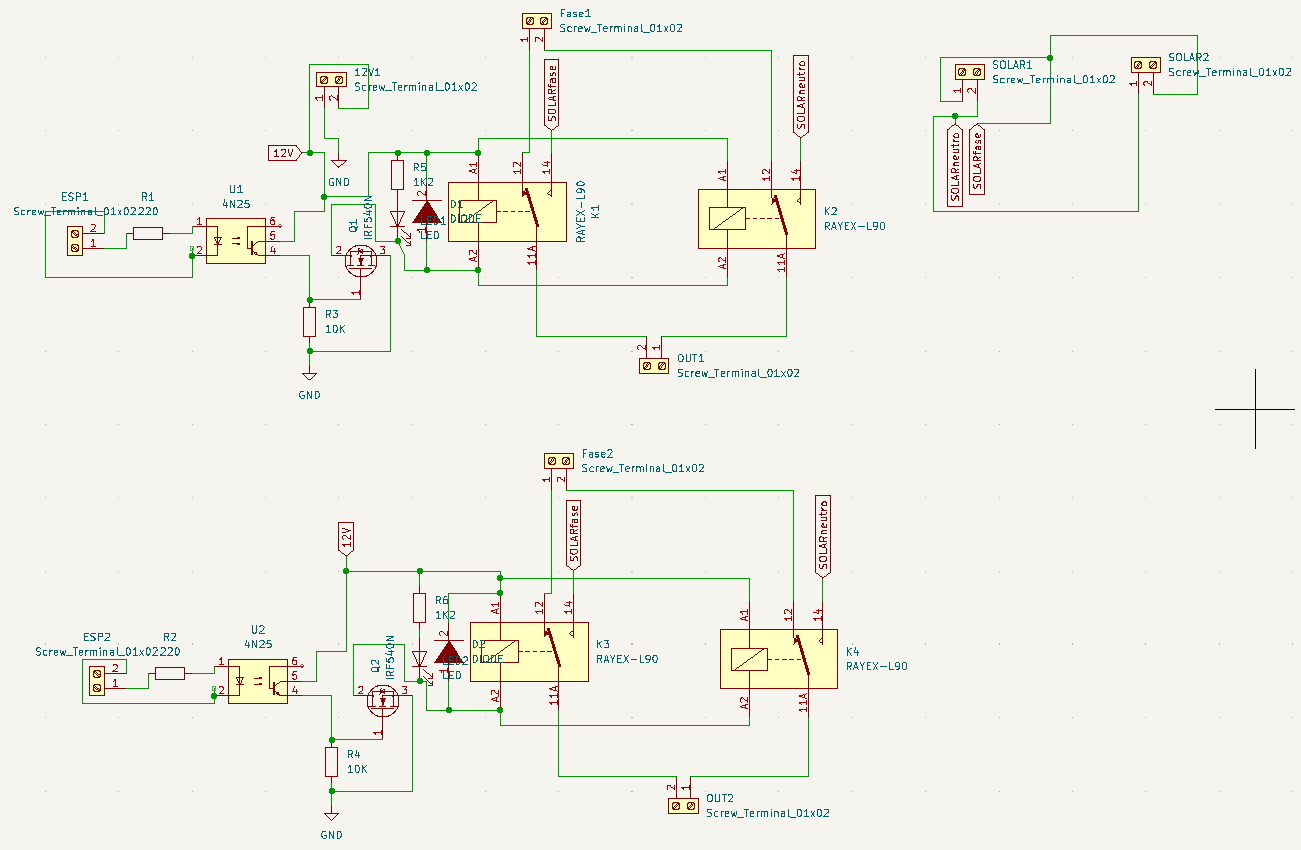
PCBs/Conmutación/Screenshot_319.png
