solarlink-ar/solarlink-web/PCBs/Medicion de corriente/Medicion de corriente SolarLink/Screenshot_7.png

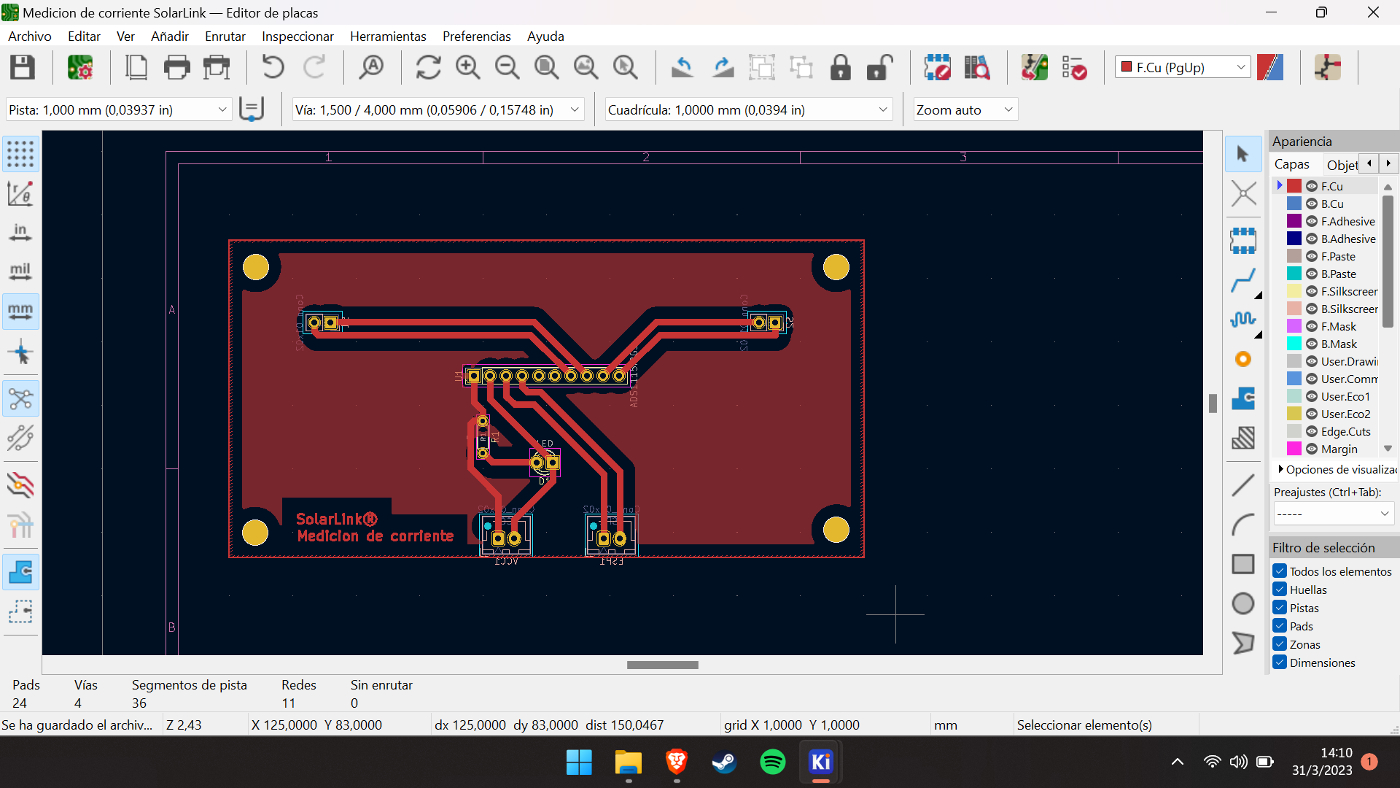
PCBs/Medicion de corriente/Medicion de corriente SolarLink/Screenshot_7.png
