solarlink-ar/solarlink-web/PCBs/Medicion de corriente/Medicion de corriente SolarLink/Screenshot_9.png

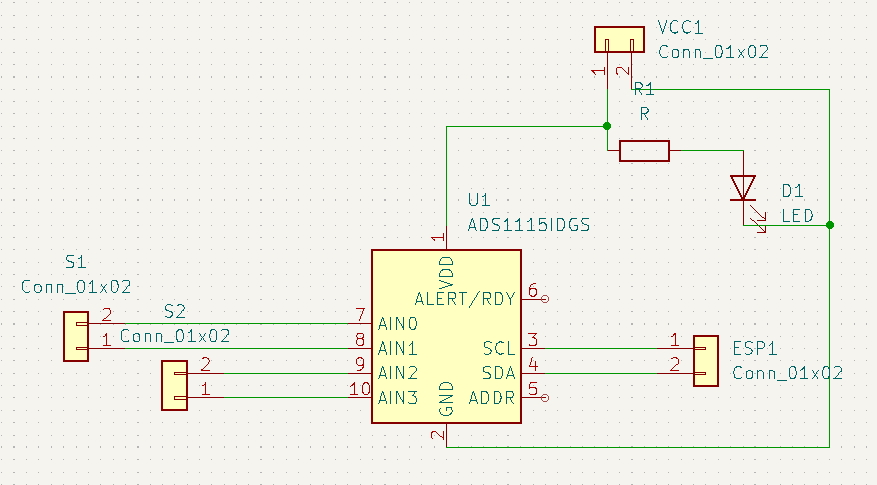
PCBs/Medicion de corriente/Medicion de corriente SolarLink/Screenshot_9.png
