solarlink-ar/solarlink-web/PCBs/Regulador de tension/Screenshot_10.png

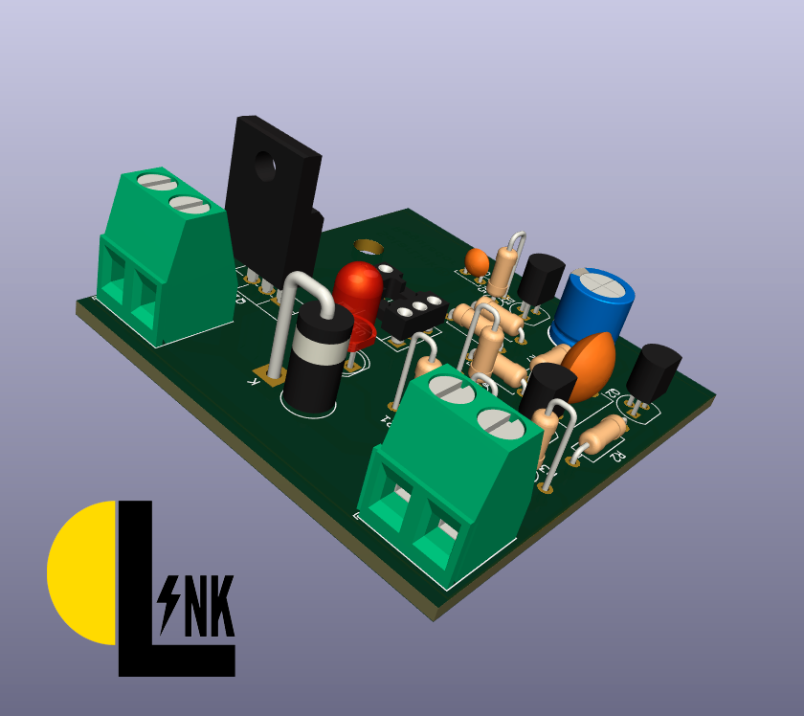
PCBs/Regulador de tension/Screenshot_10.png
