solarlink-ar/solarlink-web/Documentación/Códigos/Carpeta Tecnica Solar Link/MPPT/step-down.png

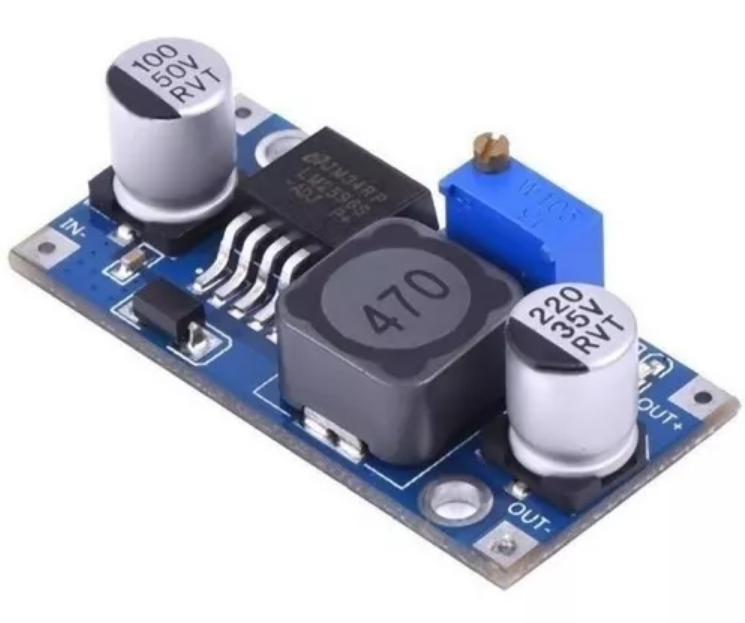
Documentación/Códigos/Carpeta Tecnica Solar Link/MPPT/step-down.png
