solarlink-ar/solarlink-web/ESP32_tablero_upython/pruebas_funcionamiento/Sensor de corriente y sensor de voltaje (consumo en potencia)/12_4 medicion de potencia con sensor de corriente y voltaje/python/Figure_1.png

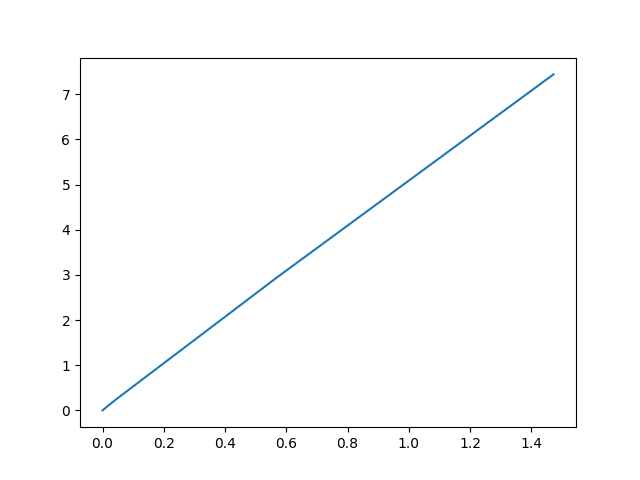
ESP32_tablero_upython/pruebas_funcionamiento/Sensor de corriente y sensor de voltaje (consumo en potencia)/12_4 medicion de potencia con sensor de corriente y voltaje/python/Figure_1.png
