solarlink-ar/solarlink-web/ESP32_tablero_upython/pruebas_funcionamiento/Sensor de corriente/20_3 midiendo corriente pico/graficos/grafico con corrientes.png

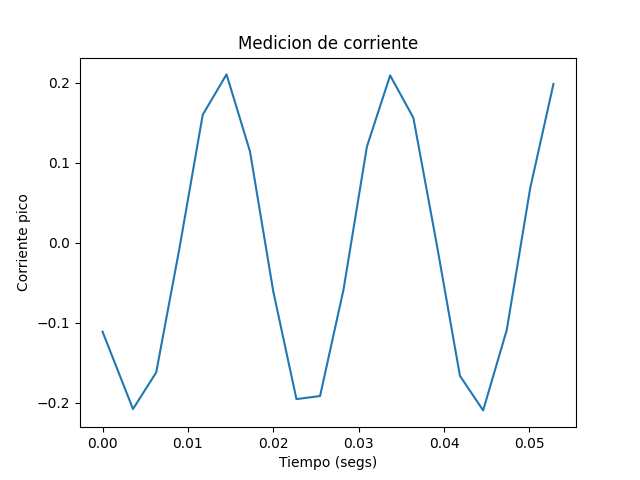
ESP32_tablero_upython/pruebas_funcionamiento/Sensor de corriente/20_3 midiendo corriente pico/graficos/grafico con corrientes.png
