solarlink-ar/solarlink-web/ESP32_tablero_upython/pruebas_funcionamiento/Sensor de corriente/27_ 3 correccion de la cte y medicion de potencia/python/respuesta del sensor.png

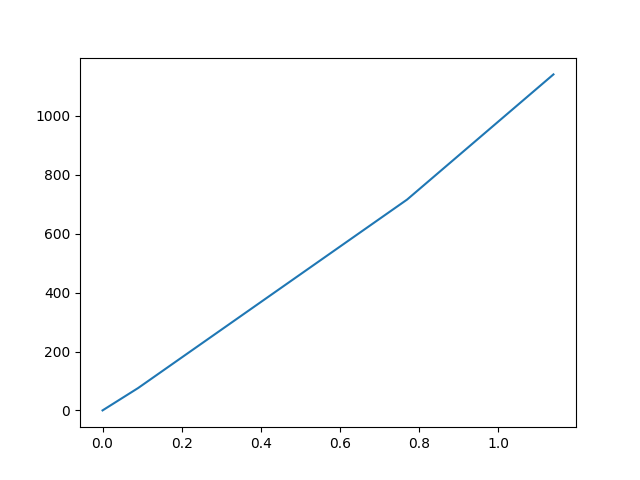
ESP32_tablero_upython/pruebas_funcionamiento/Sensor de corriente/27_ 3 correccion de la cte y medicion de potencia/python/respuesta del sensor.png
