solarlink-ar/solarlink-web/PCBs/Regulador de tension/Regulador de tension.pdf

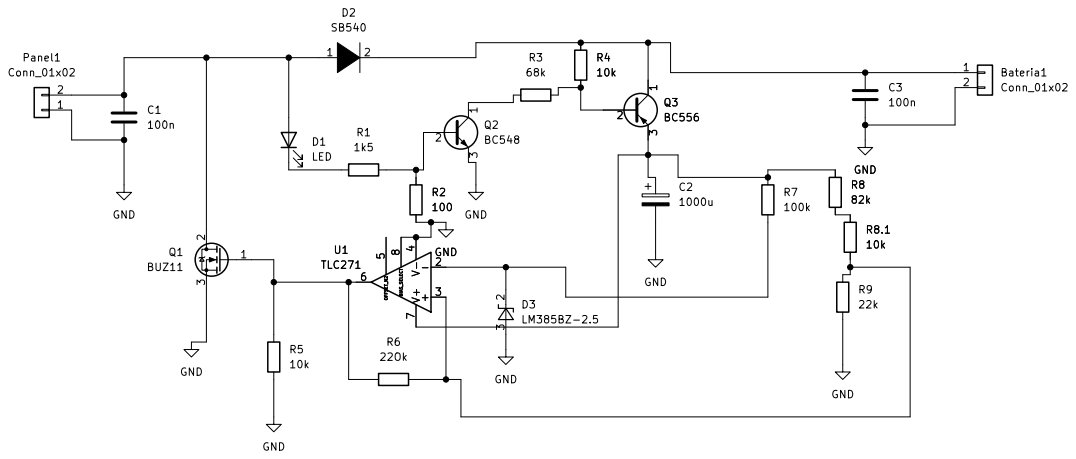
[picture p234: page 1]

File: Regulador de tension.kicad_sch Sheet: /
Id: 1/1 Title:
