solarlink-ar/solarlink-web/PCBs/Controlador MPPT/Controlador MPPT.pdf

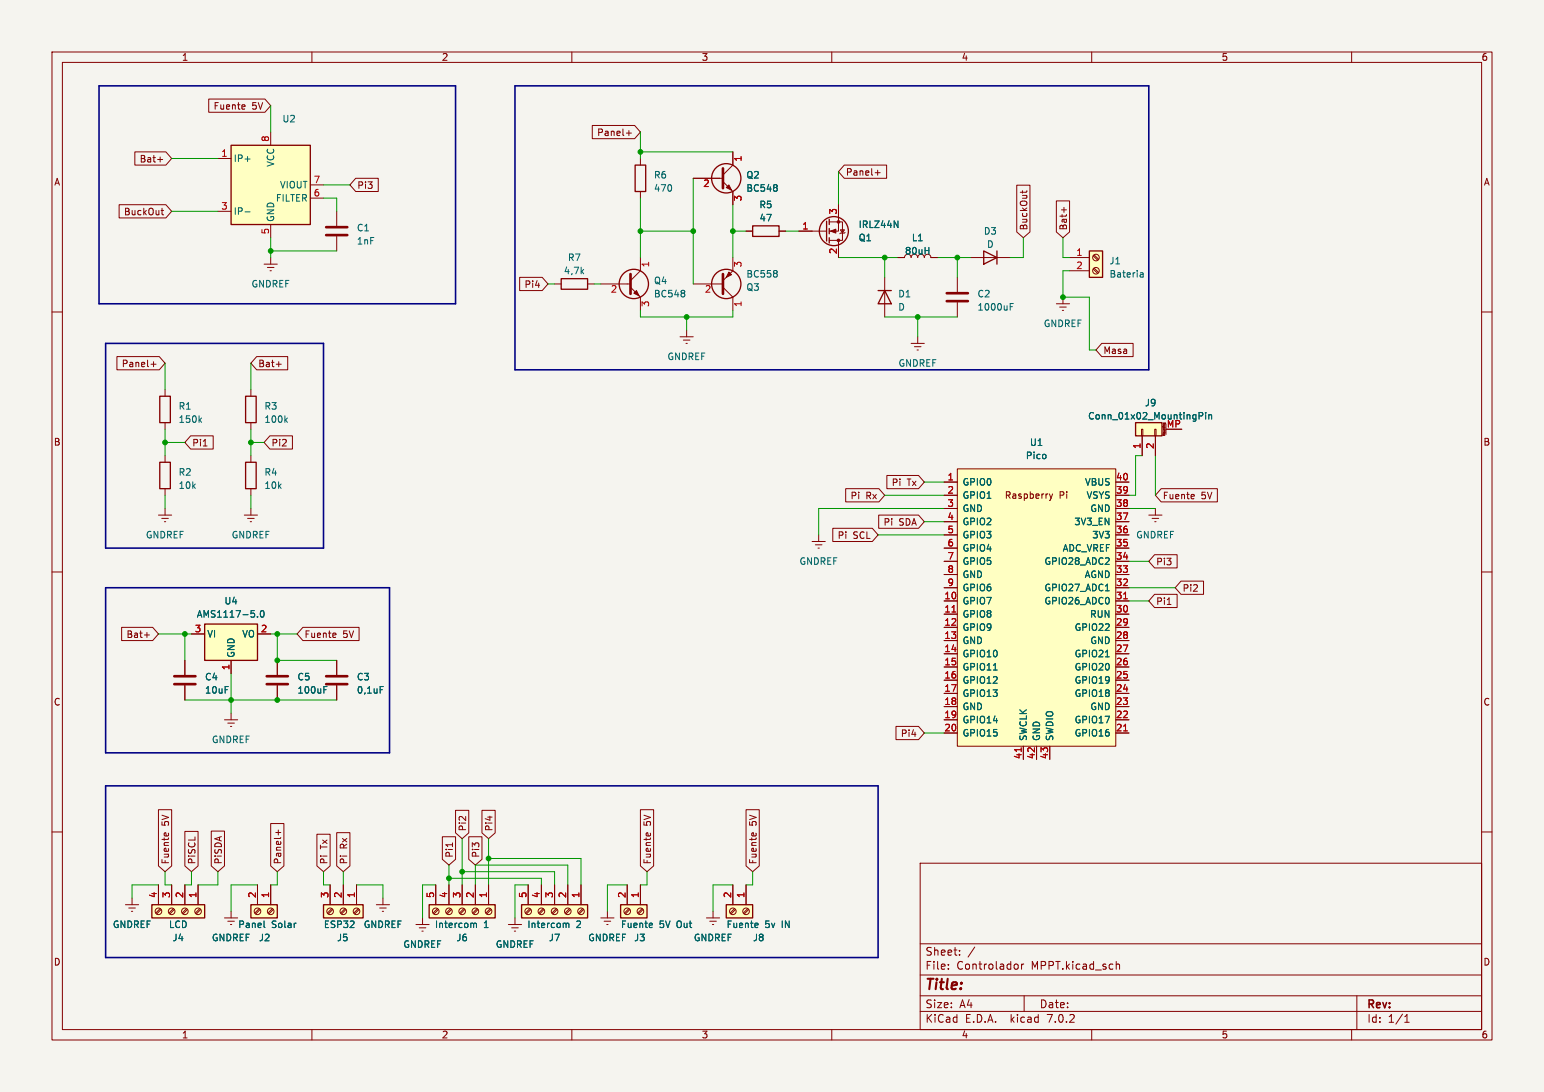
[picture p242: page 1]
