solarlink-ar/solarlink-web/PCBs/Controlador MPPT/Pi Zero Mother-B_Cu.pdf

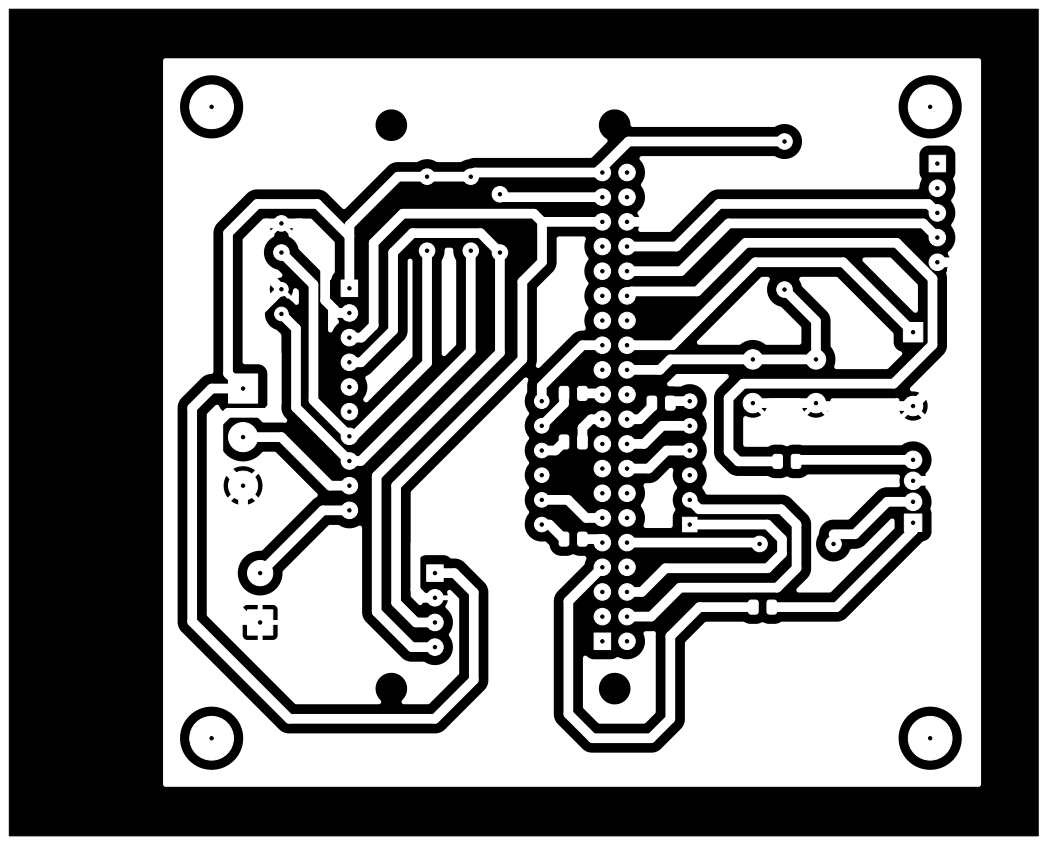
[picture p243: page 1]
