solarlink-ar/solarlink-web/PCBs/Regulador de tension/Regulador de tension-B_Cu.pdf

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

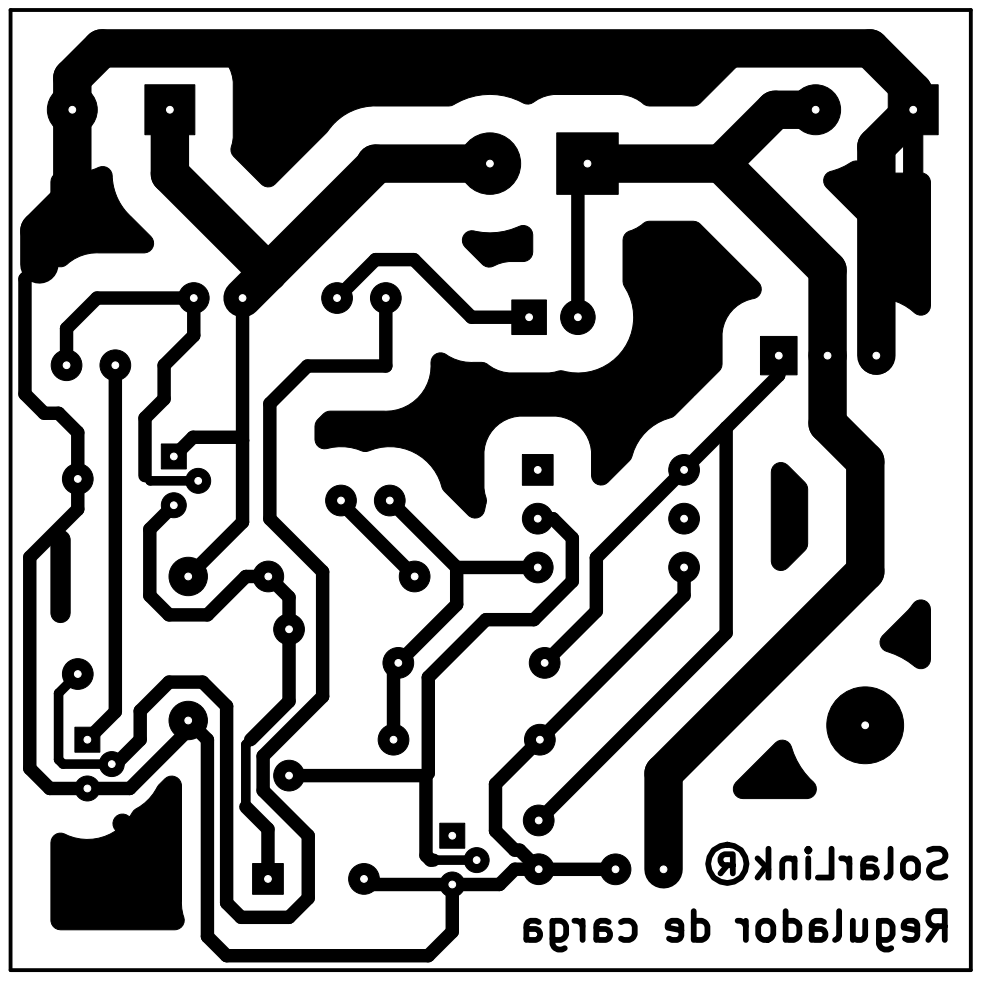
[picture p244: page 1]
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
