solarlink-ar/solarlink-web/PCBs/Regulador de tension/Regulador de tension-B_Mask.pdf

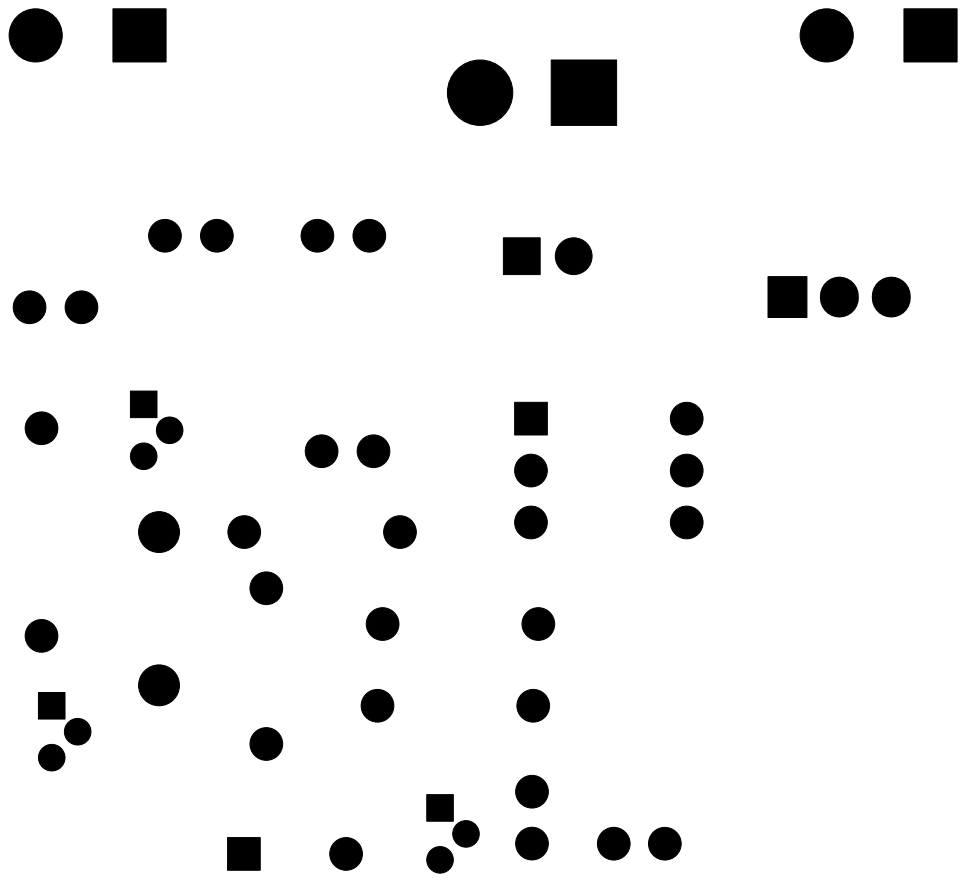
[picture p245: page 1]
