solarlink-ar/solarlink-web/PCBs/Regulador de tension/Regulador de tension-F_Cu.pdf

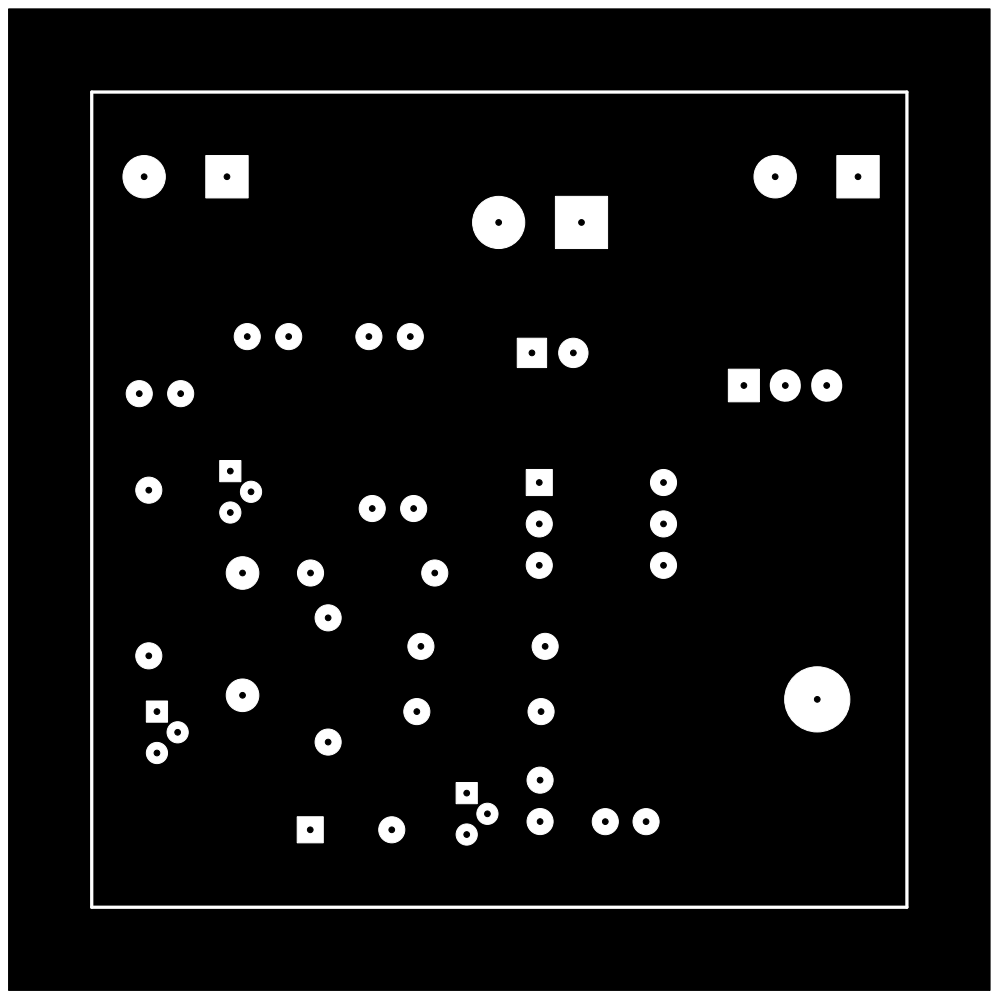
[picture p246: page 1]
