solarlink-ar/solarlink-web/PCBs/Regulador de tension/Regulador de tension-F_Silkscreen.pdf

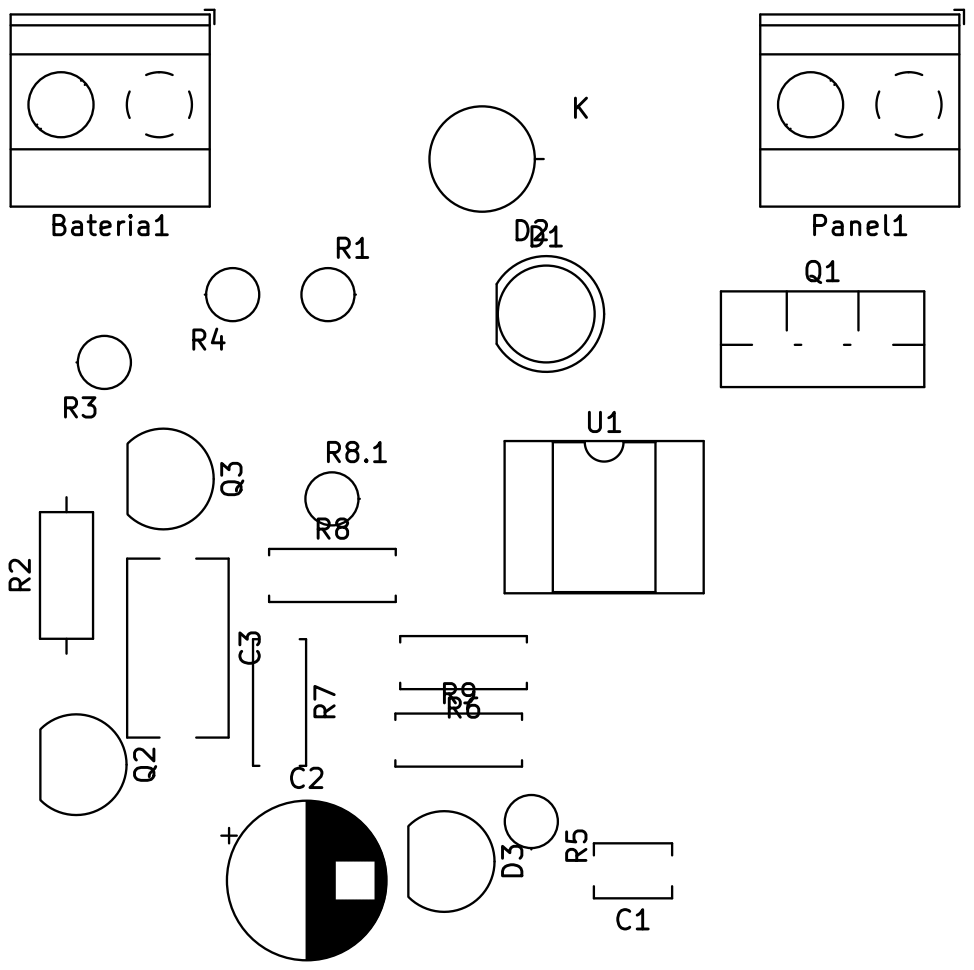
[picture p247: page 1]
