solarlink-ar/solarlink-web/PCBs/Medicion de corriente/Medicion de corriente 2.0/Medicion de corriente 2.0-B_Cu.pdf

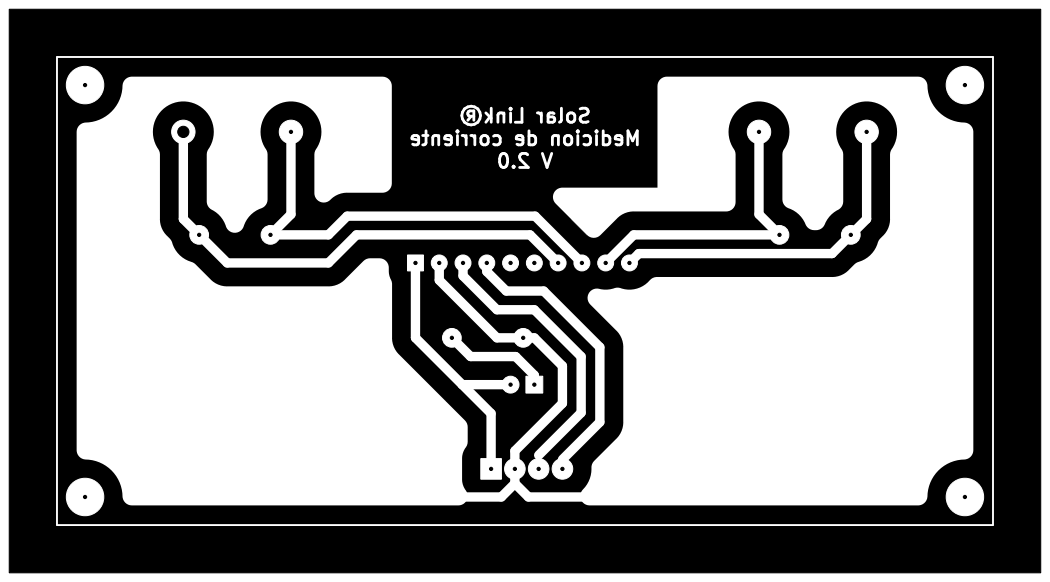
[picture p248: page 1]
