solarlink-ar/solarlink-web/PCBs/Medicion de corriente/Medicion de corriente 2.0/Medicion de corriente 2.0-B_Mask.pdf

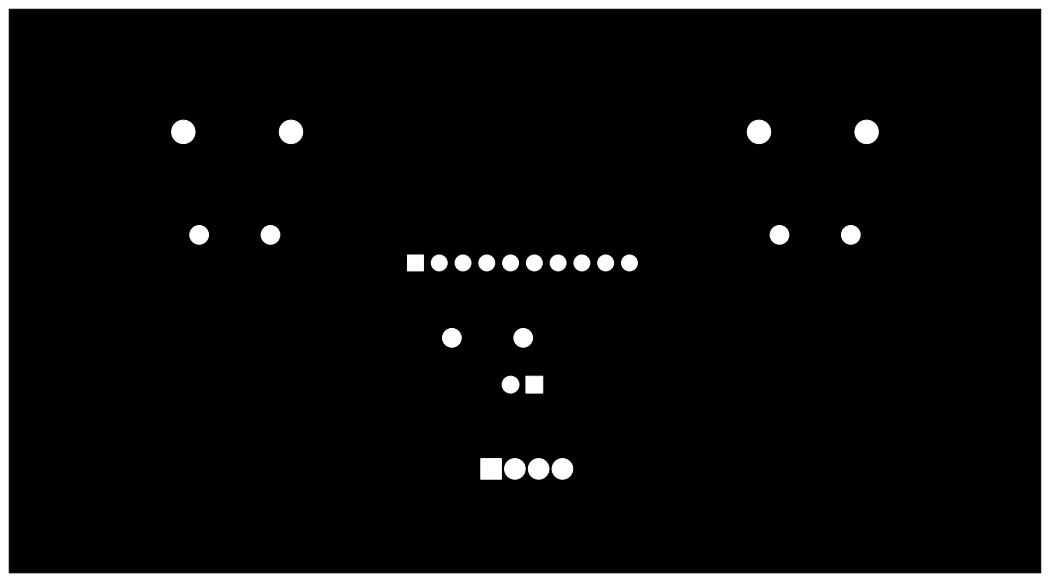
[picture p249: page 1]
