solarlink-ar/solarlink-web/PCBs/Medicion de corriente/Medicion de corriente 2.0/Medicion de corriente 2.0-B_Silkscreen.pdf

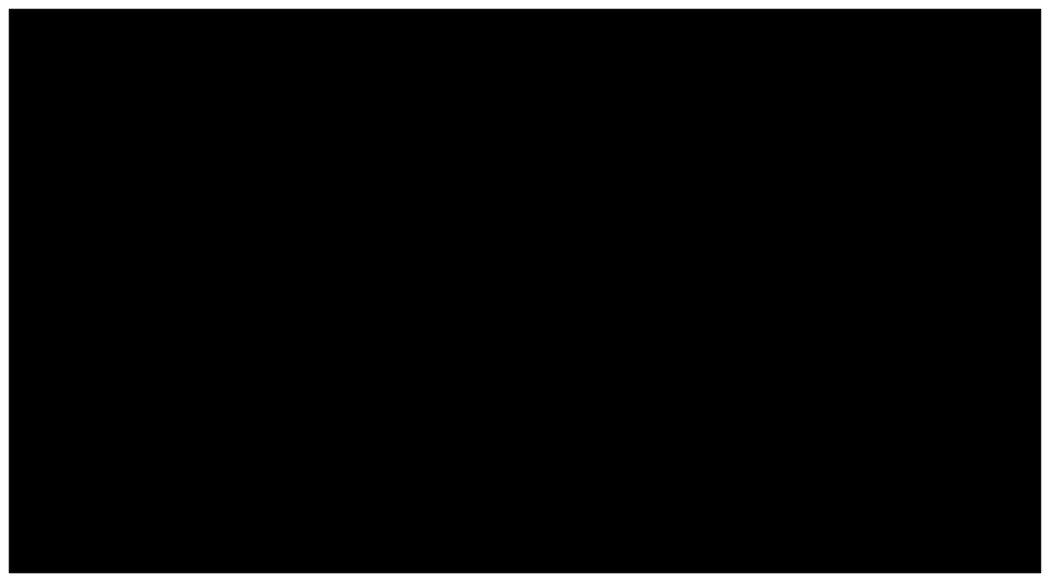
[picture p250: page 1]
