solarlink-ar/solarlink-web/PCBs/Medicion de corriente/Medicion de corriente 2.0/Medicion de corriente 2.0-F_Silkscreen.pdf

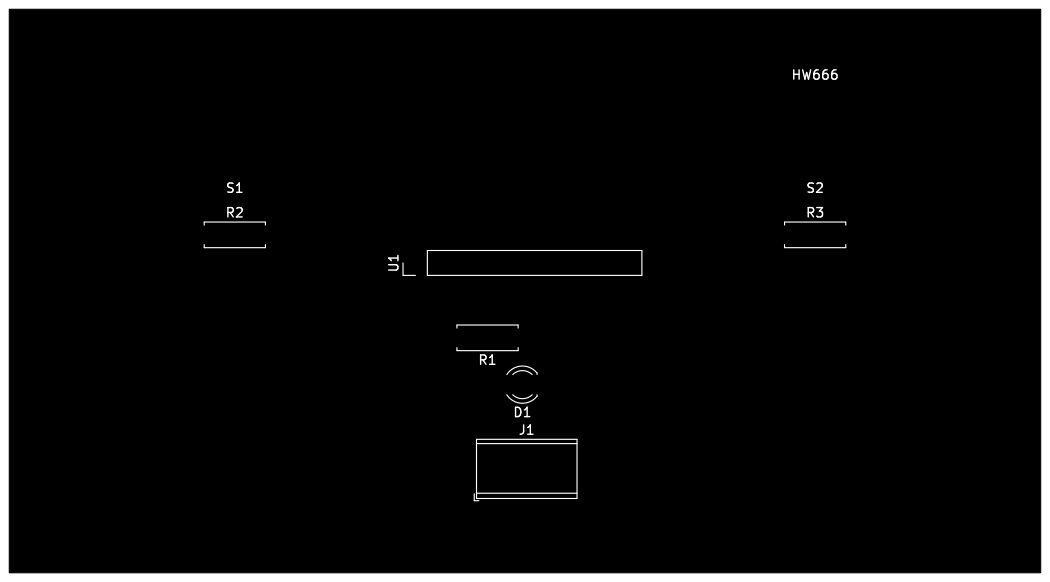
[picture p251: page 1]
