solarlink-ar/solarlink-web/PCBs/Medicion de corriente/Medicion de corriente SolarLink/Medicion de corriente SolarLink-B_Cu.pdf

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

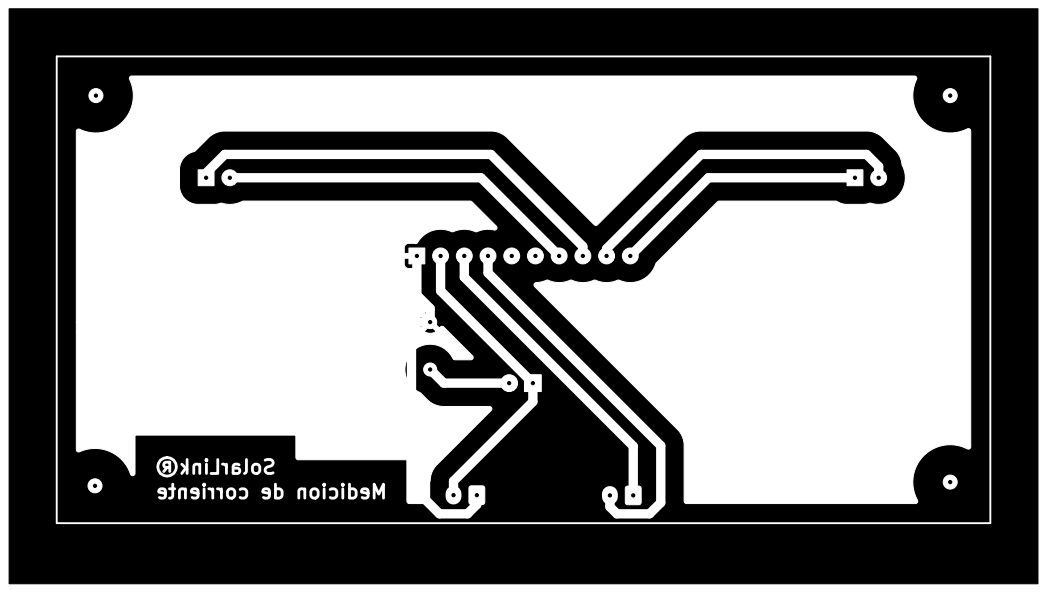
[picture p252: page 1]
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
