solarlink-ar/solarlink-web/PCBs/MotherBoard/MotherBoard 2.0/MotherBoard 2.0-B_Cu.pdf

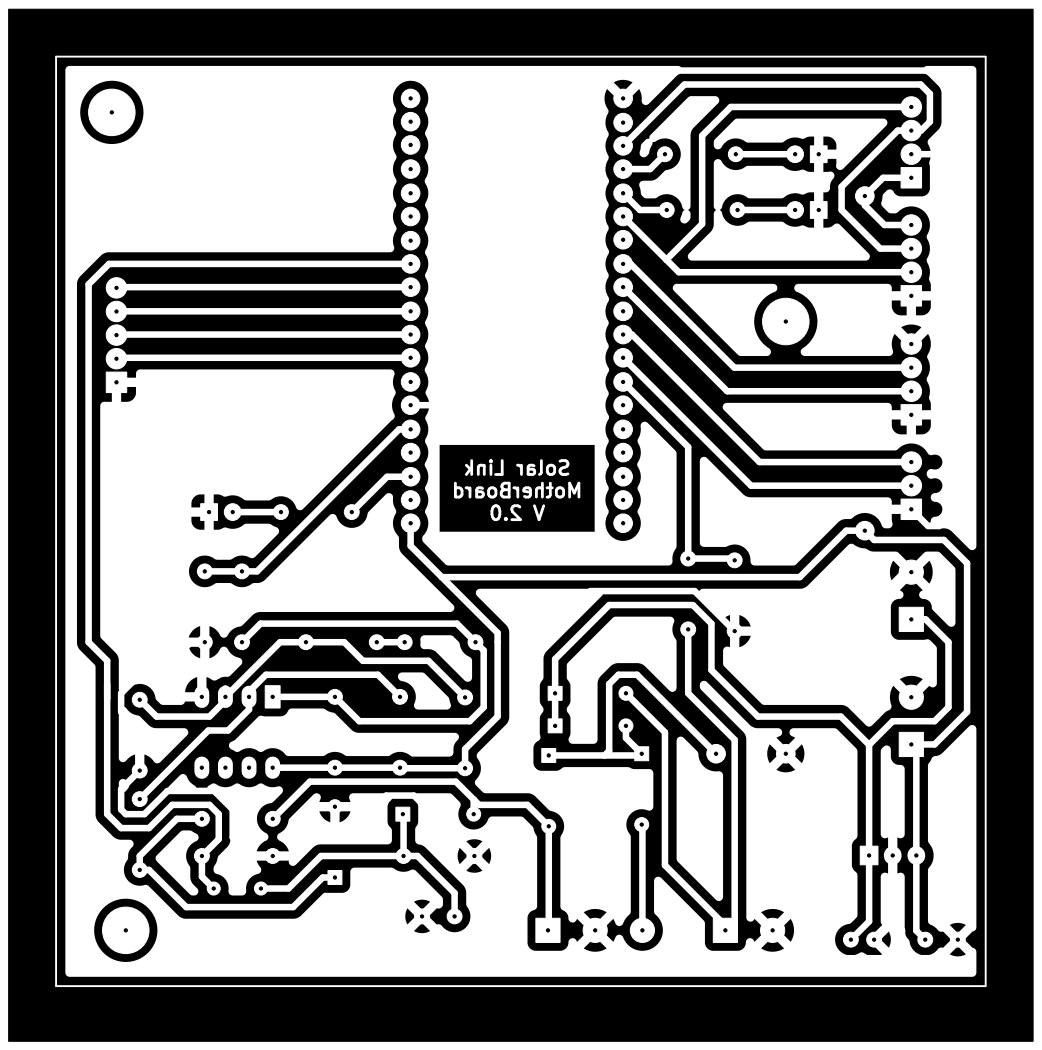
[picture p253: page 1]
