solarlink-ar/solarlink-web/PCBs/MotherBoard/MotherBoard 2.0/MotherBoard 2.0-B_Mask.pdf

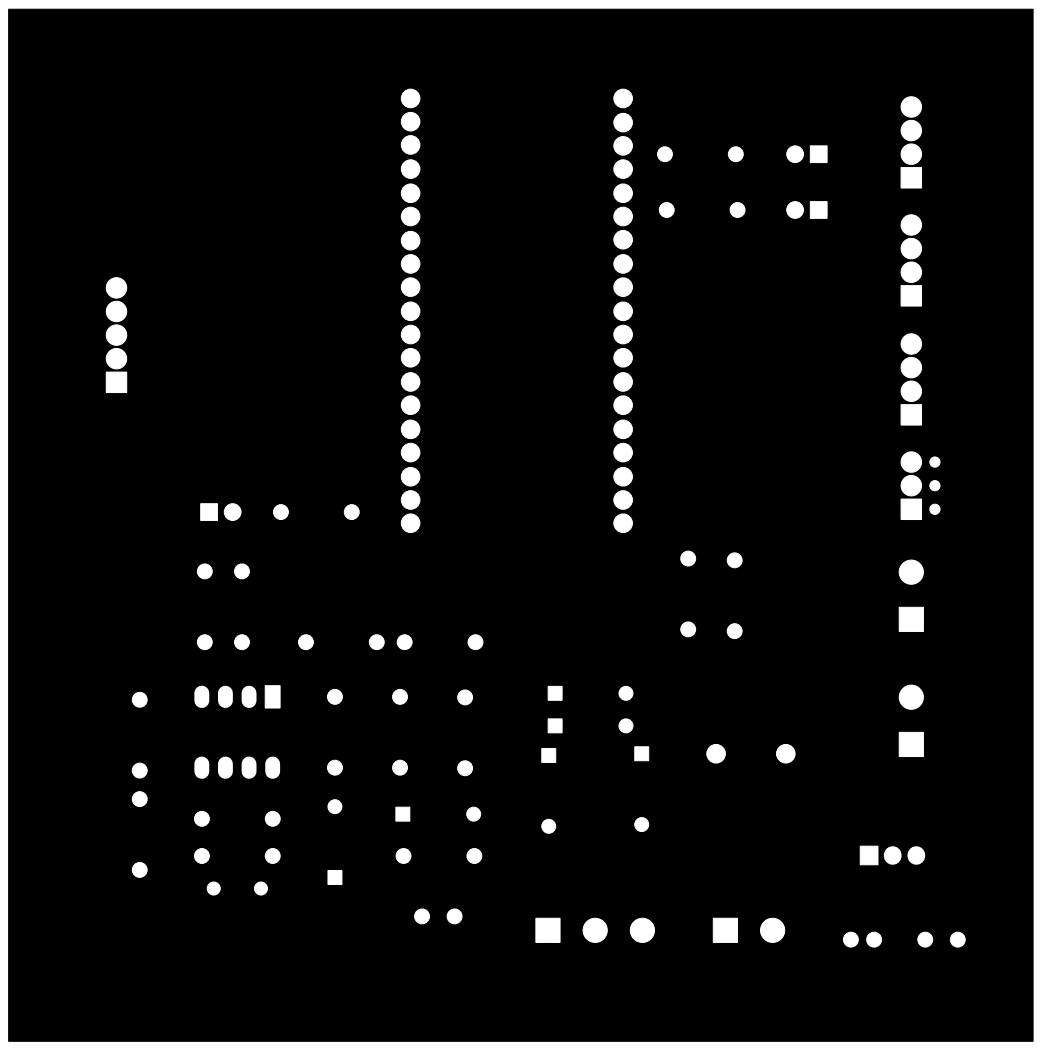
[picture p254: page 1]
