solarlink-ar/solarlink-web/PCBs/MotherBoard/MotherBoard 2.0/MotherBoard 2.0-B_Silkscreen.pdf

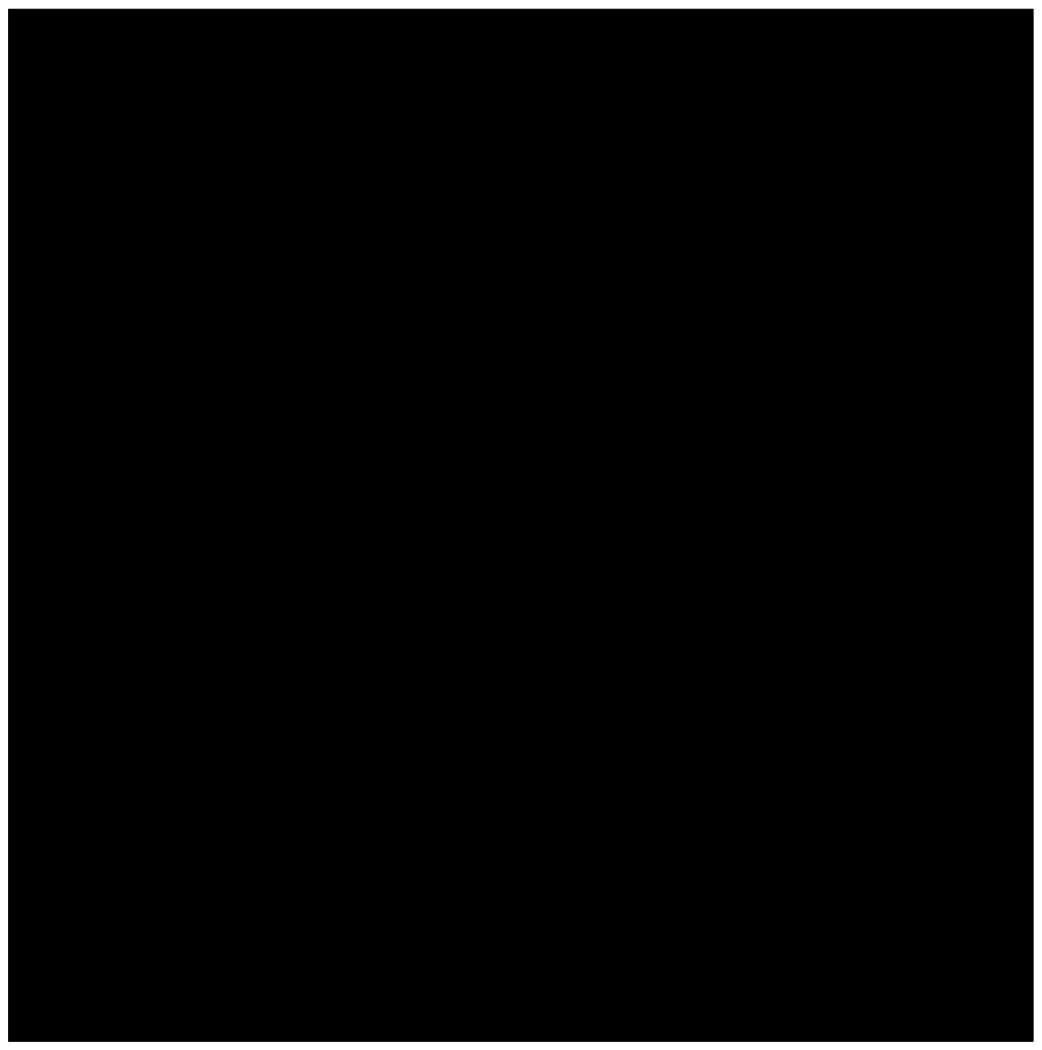
[picture p255: page 1]
