solarlink-ar/solarlink-web/PCBs/MotherBoard/MotherBoard 3.0/MotherBoard 3.0-B_Cu.pdf

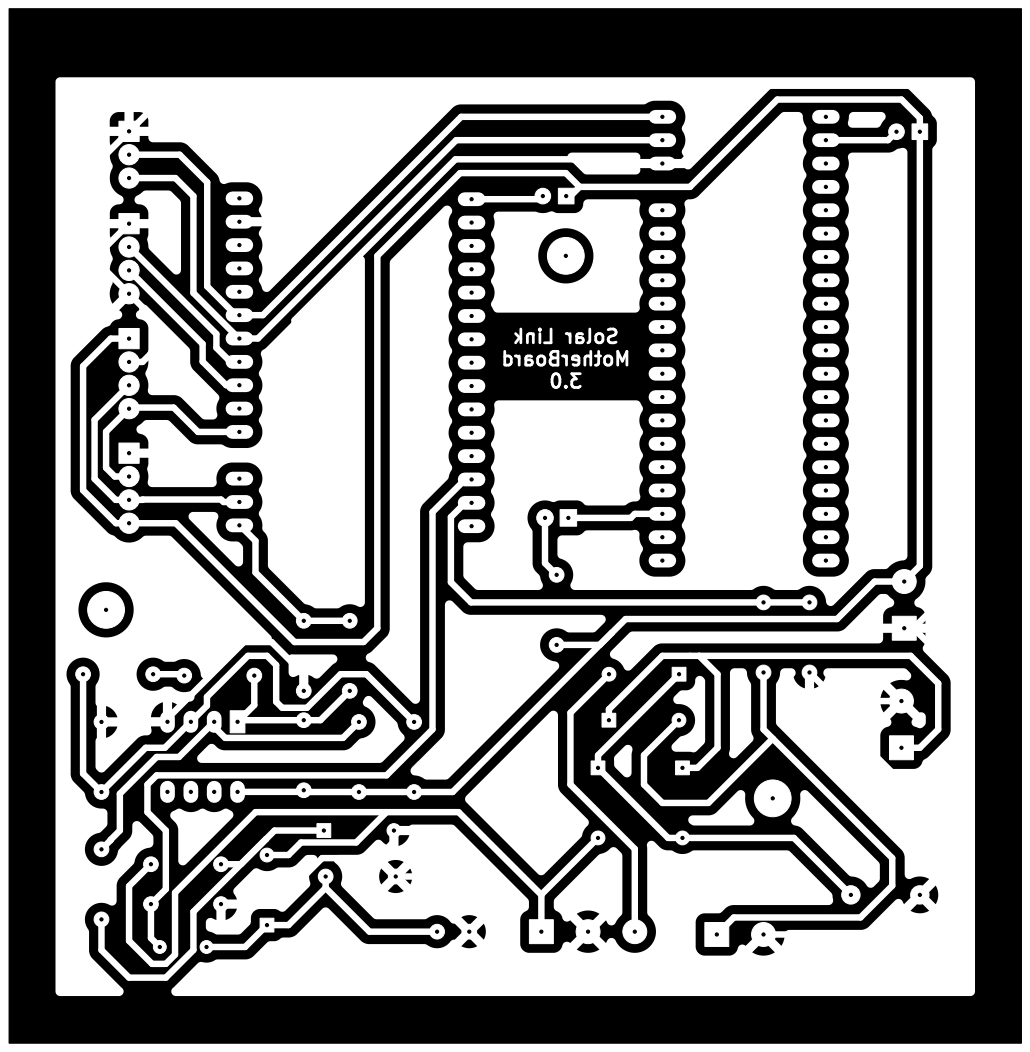
[picture p256: page 1]
