solarlink-ar/solarlink-web/PCBs/MotherBoard/MotherBoard 3.0/MotherBoard 3.0-B_Mask.pdf

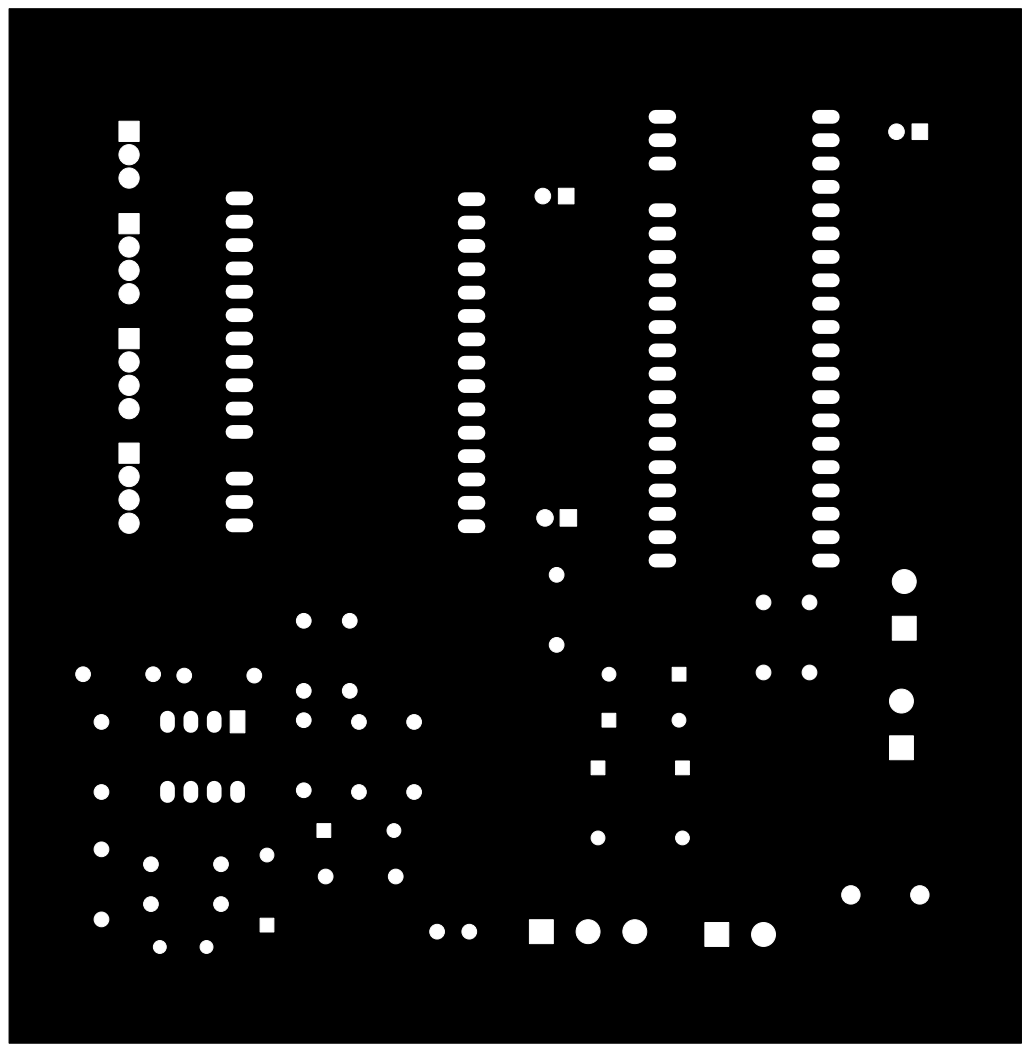
[picture p257: page 1]
