solarlink-ar/solarlink-web/PCBs/MotherBoard/MotherBoard 3.0/MotherBoard 3.0-B_Silkscreen.pdf

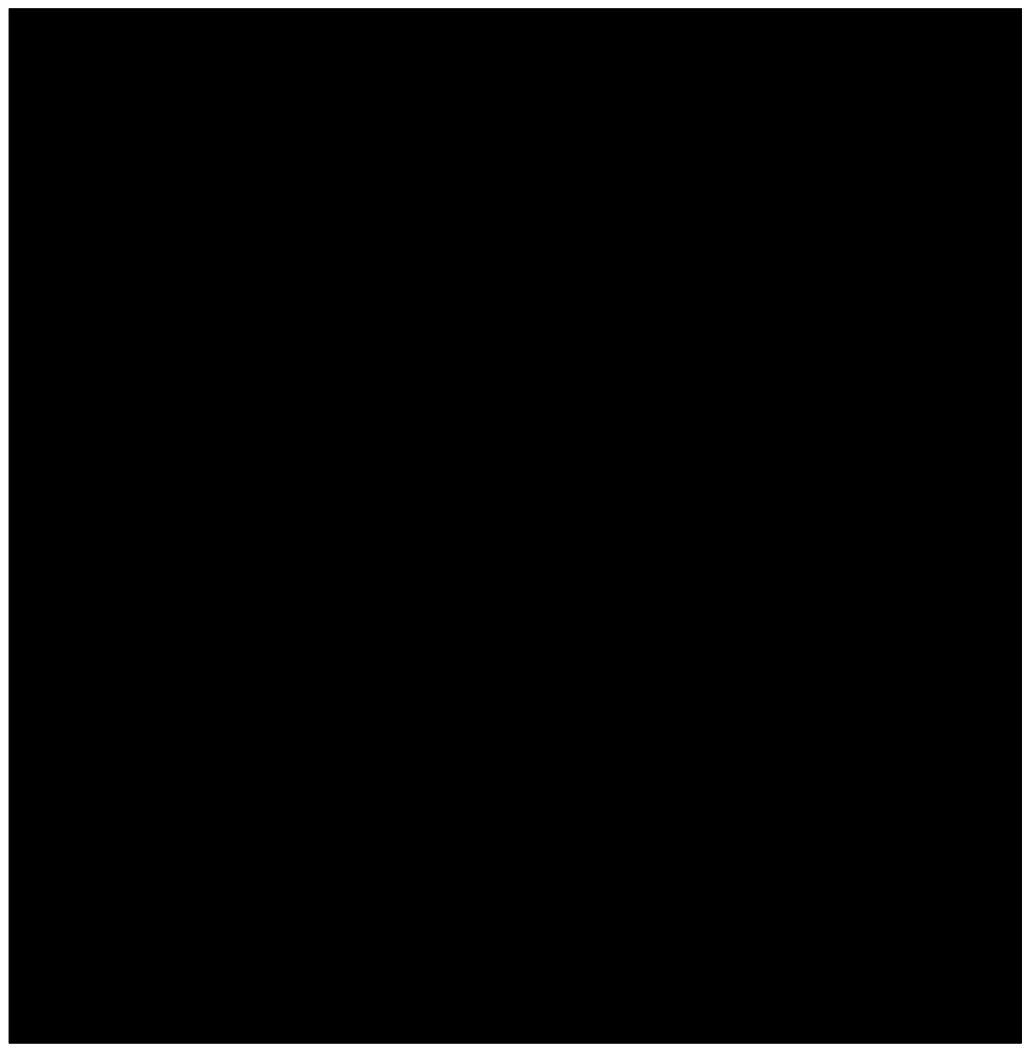
[picture p258: page 1]
