solarlink-ar/solarlink-web/PCBs/MotherBoard/MotherBoard/MotherBoard-B_Cu.pdf

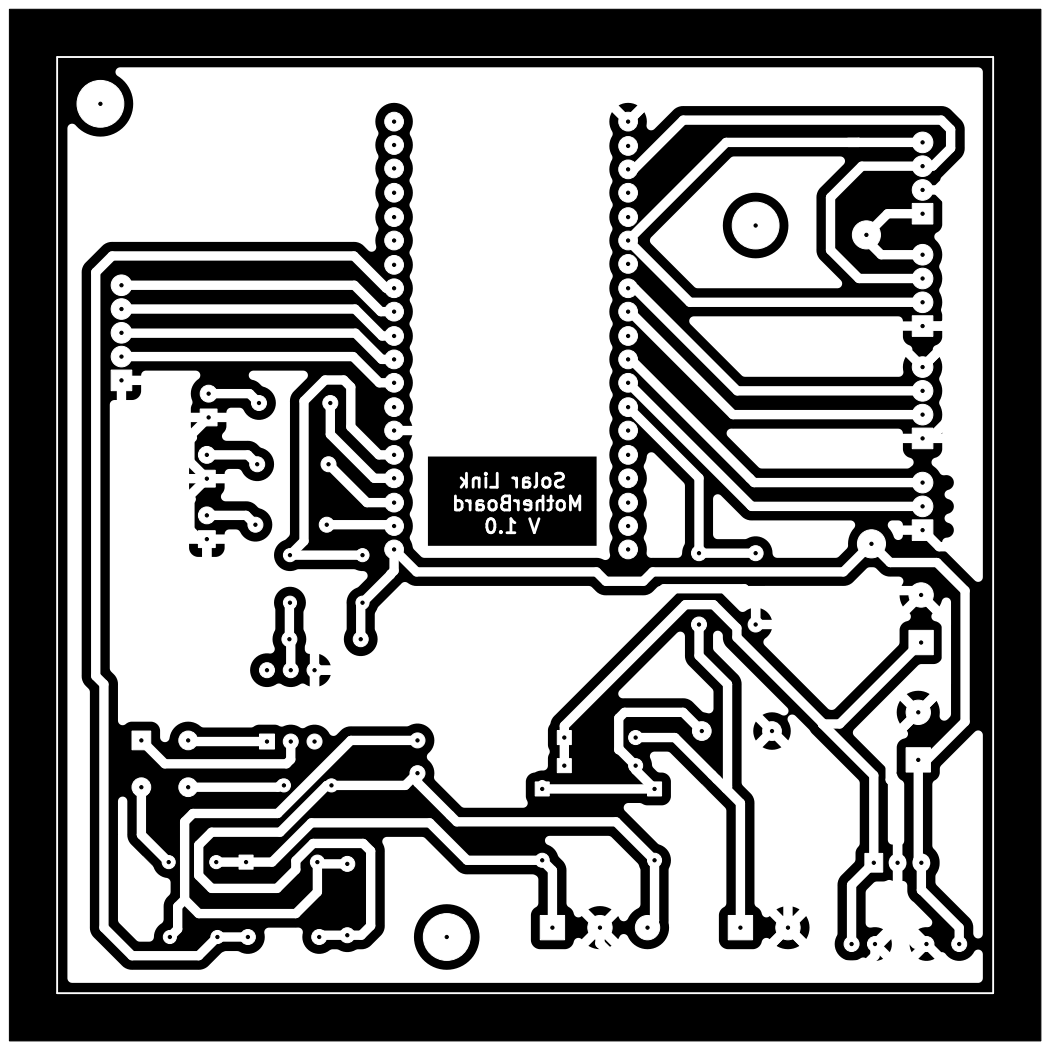
[picture p259: page 1]
