solarlink-ar/solarlink-web/PCBs/MotherBoard/MotherBoard/MotherBoard-B_Mask.pdf

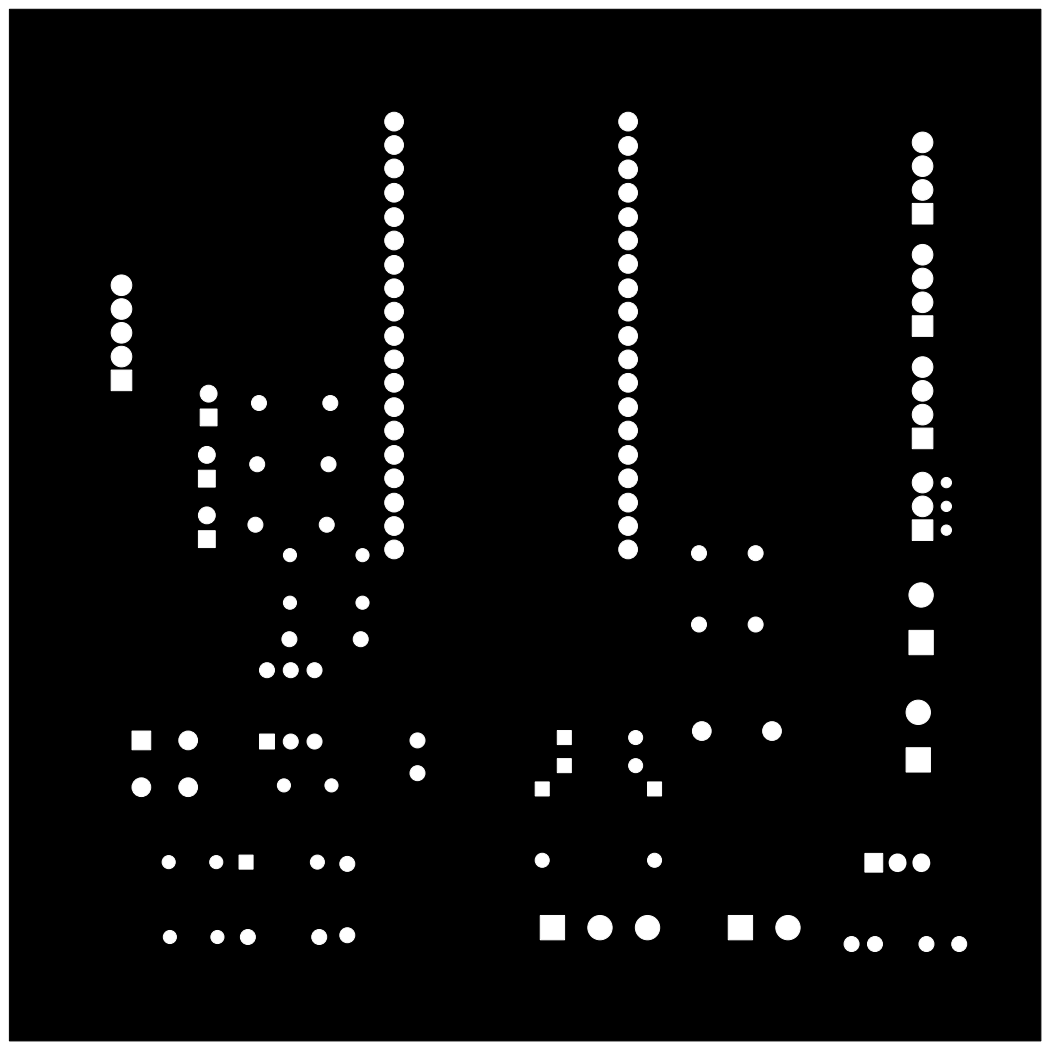
[picture p260: page 1]
