solarlink-ar/solarlink-web/PCBs/MotherBoard/MotherBoard/MotherBoard-B_Silkscreen.pdf

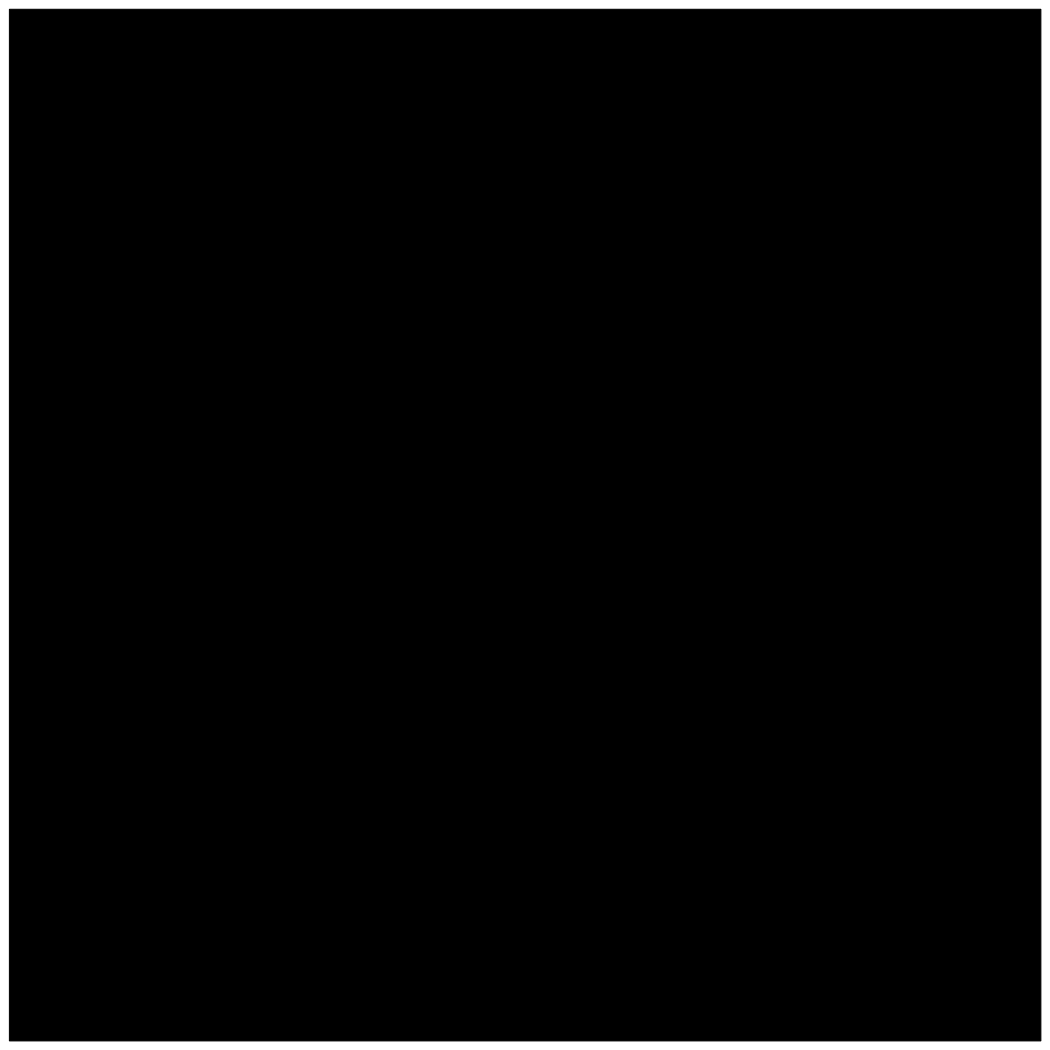
[picture p261: page 1]
