solarlink-ar/solarlink-web/PCBs/MotherBoard/MotherBoard/MotherBoard-F_Mask.pdf

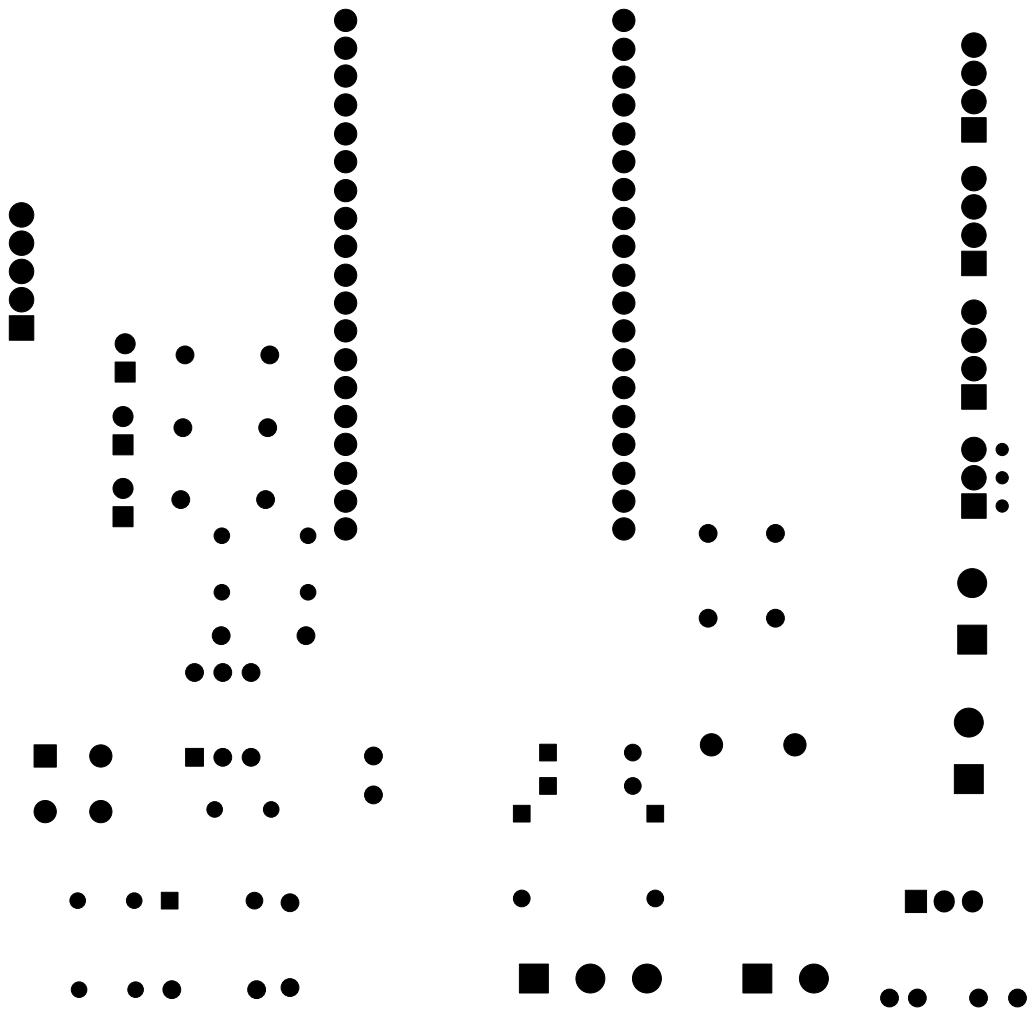
[picture p262: page 1]
