solarlink-ar/solarlink-web/PCBs/MotherBoard/MotherBoard/MotherBoard-F_Silkscreen.pdf

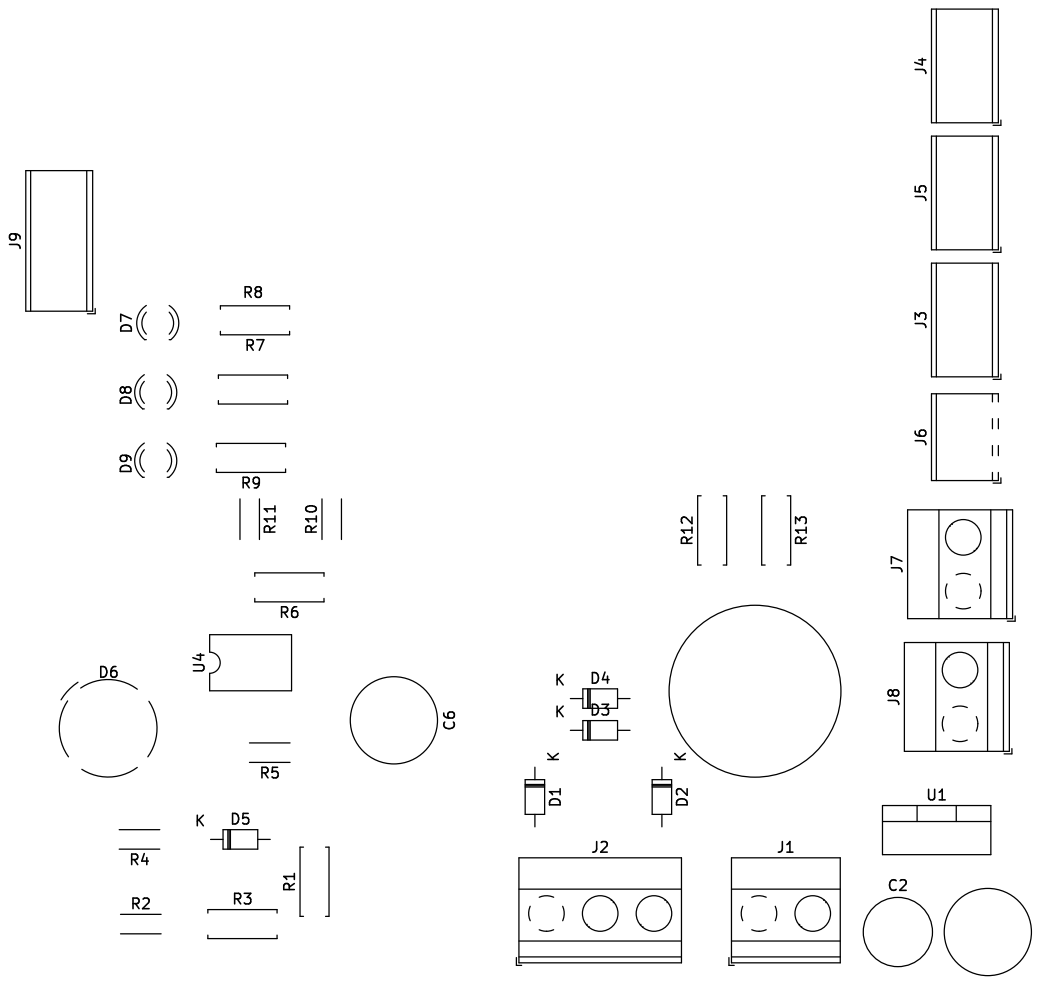
[picture p263: page 1]
