solarlink-ar/solarlink-web/ESP32_tablero_upython/main/bare_metal_thread_main.py

from solarlink import Solarlink
import machine, time as utime, json, math, ads1115, network
from machine import Pin, ADC, I2C, Timer, UART
from lcd_api import LcdApi
from i2c_lcd import I2cLcd
import urequests as requests
import ujson as json
import _thread

lock = False
def post(url, data):
    global lock
    payload = json.dumps(data)
    if not lock:
        try:
            lock = True
            r = requests.post(url, data=payload, timeout=20)
            utime.sleep(10)
            lock = False
        except:
            lock = False
            _thread.exit()

    else:
        _thread.exit()
        
def post_hora(url, data):
    payload = json.dumps(data)
    done = False
    while not done:
        try:
            r = requests.post(url, data=payload, timeout=20)
            done = True
        except:
            pass


#
#
solarlink = Solarlink()
#
#
sol = bytearray([0x00,0x00,0x15,0x0E,0x1B,0x0E,0x15,0x00])
solarlink.lcd.custom_char(0, sol)

while 1:
    valores = solarlink.medicion_default_segundo()

    solarlink.lcd.hal_write_command(LcdApi.LCD_HOME)
    solarlink.lcd.hide_cursor()

    solarlink.lcd.custom_char(0, sol)
    if solarlink.l1:
        sol_l1 = chr(0)
    else:
        sol_l1 = ' '
    if solarlink.l2:
        sol_l2 = chr(0)
    else:
        sol_l2 = ' '
    solarlink.lcd.move_to(0,0)
    solarlink.lcd.putstr(f"{sol_l1}" + "    " + f"Vin:{valores['voltaje']} V" + "     " + f"{sol_l2}")
    solarlink.lcd.move_to(0,1)
    solarlink.lcd.putstr(f"LINEA1        LINEA2")
    solarlink.lcd.move_to(0,2)
    solarlink.lcd.putstr(f"%.2f A"% (valores["corriente_l1"]) + "        " + "%.2f A" % (valores["corriente_l2"]))
    solarlink.lcd.move_to(0,3)
    solarlink.lcd.putstr('{:0>4d} W'.format(valores["consumo_l1"]) + "        " + '{:0>4d} W'.format(valores["consumo_l2"]))
    

    
    voltaje = valores["voltaje"]
    corriente_l1 = valores["corriente_l1"]
    corriente_l2 = valores["corriente_l2"]
    consumo_l1 = valores["consumo_l1"]
    consumo_l2 = valores["consumo_l2"]
    
        
    trigger = solarlink.trigger

    # logica de conmutacion
    if consumo_l1 + consumo_l2 < trigger:
        solarlink.conmutador(l1 = True, l2 = True)
    else:
        if consumo_l1 < trigger and consumo_l2 < trigger:
            if consumo_l1 > consumo_l2:
                solarlink.conmutador(l1 = True, l2 = False)
            else:
                solarlink.conmutador(l1=False, l2=True)

        if consumo_l1 > trigger and consumo_l2 > trigger:
            solarlink.conmutador(l1=False, l2=False)
        elif consumo_l1 > trigger and consumo_l2 < trigger:
            solarlink.conmutador(l1=False, l2=True)
        elif consumo_l1 < trigger and consumo_l2 > trigger:
            solarlink.conmutador(l1=True, l2=False)

    payload = {"username": solarlink.username, "password": solarlink.password,
                                "voltaje": solarlink.medicion["voltaje"],
                                "consumo_l1": solarlink.medicion["consumo_l1"],
                                "consumo_l2": solarlink.medicion["consumo_l2"],
                                "solar_l1": solarlink.l1,
                                "solar_l2": solarlink.l2}

    try:
        _thread.start_new_thread(post, (solarlink.url + "/user/tiempo-real/", payload))
    except:
        pass
        
    if solarlink.hora_inicial != solarlink.rtc.datetime()[4]:
        time = solarlink.rtc.datetime()
        payload = {"username": solarlink.username, "password": solarlink.password,
                "voltaje_hora_red": solarlink.acumulacion_voltaje_red / solarlink.indice_mediciones,
                "consumo_hora_solar": solarlink.acumulacion_consumo_solar / solarlink.indice_mediciones,
                "consumo_hora_red": solarlink.acumulacion_consumo_red / solarlink.indice_mediciones,
                "consumo_l1_solar": solarlink.acumulacion_consumo_l1_solar / solarlink.indice_mediciones,
                "consumo_l1_proveedor": solarlink.acumulacion_consumo_l1_proveedor / solarlink.indice_mediciones,
                "consumo_l2_solar": solarlink.acumulacion_consumo_l2_solar / solarlink.indice_mediciones,
                "consumo_l2_proveedor": solarlink.acumulacion_consumo_l2_proveedor / solarlink.indice_mediciones,
                "solar_ahora": (solarlink.l1 or solarlink.l2)}
        
        solarlink.acumulacion_consumo_l1_proveedor = 0
        solarlink.acumulacion_consumo_l1_solar = 0
        solarlink.acumulacion_consumo_l2_proveedor = 0
        solarlink.acumulacion_consumo_l2_solar = 0
        solarlink.acumulacion_consumo_red = 0
        solarlink.acumulacion_consumo_solar = 0
        solarlink.acumulacion_voltaje_red = 0
        solarlink.indice_mediciones = 0
        solarlink.hora_inicial = time[4]

        try:
            _thread.start_new_thread(post_hora, (solarlink.url + "/user/load-data/", payload))
        except:
            pass
