solarlink-ar/solarlink-web/ESP32_tablero_upython/Librerias/solarlink_online.py

import machine, time, json, math, ads1115, network
from machine import Pin, ADC, I2C, Timer, UART, RTC,
from lcd_api import LcdApi
from i2c_lcd import I2cLcd
import urequests as requests
import ntptime
import _thread

class Solarlink(object):
    
    ######################################################################################################
    ######################################################################################################
    ######################################## CONSTRUCTOR #################################################
    ######################################################################################################
    ######################################################################################################

    def __init__(self):

        ################################### ADC EXTERNO PARAMS ###########################################

        # direccion i2c ADC externo
        self.i2c_corriente_dir = 72
        # scl
        self.scl = 22
        # sda
        self.sda = 21
        # freq i2c
        self.freq = 400000
        # gain sensor
        self.gain = 0
        # pendiente de sensor de corriente
        self.pendiente_corriente = 10.1288571642

        ################################### ADC INTERNO PARAMS ###########################################

        # pin adc sensor voltaje
        self.adc_pin = 33
        # atenuacion ADC
        self.atten = ADC.ATTN_2_5DB
        # referencia sensor voltaje
        self.ref = 221 / 0.5150402
        

        ######################################### INITS ##################################################

        # i2c init
        self.i2c = I2C(1, scl=Pin(self.scl), sda=Pin(self.sda), freq=self.freq)
        # ADC externo init
        self.ads1115 = ads1115.ADS1115(self.i2c, self.i2c_corriente_dir, self.gain)
        # ADC en el pin init
        self.adc = ADC(Pin(self.adc_pin, Pin.IN))
        # atenuacion ADC
        self.adc.atten(self.atten)
        # display init
        self.lcd = I2cLcd(self.i2c, 0x27, 4, 20)


        ################################# TIMER Y CALLBACK ATTR ##########################################

        # timer 0
        self.timer0 = None
        # trigger fin mediciones
        self.fin_mediciones = False

        
        ################################## MEDICION POR SEG ATTR #########################################

        # medicion final
        self.medicion = None

        #################################### CONMUTACION #################################################
        
        self.pin_l1 = Pin(19, Pin.OUT)
        self.pin_l2 = Pin(18, Pin.OUT)
        self.pin_cruce = Pin(13, Pin.IN, pull=None)
        self.pin_cruce.irq(trigger=Pin.IRQ_RISING, handler=self.callback_conmutacion)
        

        self.trigger = 400

        self.pedido_conmutacion = False

        self.l1 = True
        self.l2 = True
        
        #################################### USUARIO Y CONTRASEÑA #######################################

        self.username = "helyivan"
        self.password = "12345678"
        self.url = "http://192.168.111.250:8080"

        #################################### RTC ######################################################
        #ntptime.settime()
        
        self.rtc = RTC()
        ntptime.settime()
        tm = time.localtime(time.mktime(time.localtime()) -3*3600)
        tm = tm[0:3] + (0,) + tm[3:6] + (0,)
        self.rtc.datetime(tm)
        #self.rtc.datetime((2023, 11, 8, 2, 7, 59, 0, 0))
        print(self.rtc.datetime())

        #################################### POSTEO ######################################################

        self.acumulacion_voltaje_red = 0
        self.acumulacion_consumo_red = 0
        self.acumulacion_consumo_solar = 0

        self.acumulacion_consumo_l1_solar = 0
        self.acumulacion_consumo_l1_proveedor = 0

        self.acumulacion_consumo_l2_solar = 0
        self.acumulacion_consumo_l2_proveedor = 0

        self.indice_mediciones = 0

        self.hora_inicial = self.rtc.datetime()[4]
        
        self.timer1 = Timer(1).init(period=10000, mode=Timer.PERIODIC, callback=self.callback_posteo)
        
        self.tiempo_real = False


    #####################################################################################################
    #####################################################################################################
    ########################################## METODOS ##################################################
    #####################################################################################################
    #####################################################################################################


    ##################################### CALLBACK TIMER0 ###############################################

    def callback_fin_mediciones(self, t):
        self.fin_mediciones = True
    
    ##################################### CALLBACK TIMER1 ###############################################
        
    def callback_posteo(self, t):
        self.tiempo_real = True
        
    ##################################### CALLBACK CONMUT ###############################################
    
    def callback_conmutacion(self, pin):
        if self.pedido_conmutacion:
            # espero 10ms, tiempo de conmutacion del relé
            #time.sleep_ms(10)
            # switcheo pines al estado elegido
            self.pin_l1(self.l1)
            self.pin_l2(self.l2)
            self.pedido_conmutacion = False
            


    ############################### CORRIENTE ADC EN DIFERENCIAL ########################################

    # medicion de sensor de corriente en el instante 
    def corriente_dif_read(self, pin_a, pin_b):
        # medicion sensor de corriente con ADC externo
        medicion = self.ads1115.raw_to_v(self.ads1115.read(7, pin_a, pin_b))
        # traspaso a RMS
        corriente = self.pendiente_corriente * medicion / math.sqrt(2)

        return corriente

    ##################################### VOLTAJE ADC INTERNO ###########################################

    # medicion de sensor de voltaje en el instante
    def voltaje_read(self):
        # mido sensor de voltaje en el pin ADC, valor en RMS
        voltaje = self.adc.read_uv() / 1000000 * self.ref

        return voltaje
    
    ################################### MEDICION COMPLETA 1 SEG #########################################

    def medicion_default_segundo(self):

        # timer 0 init, timer de fin de mediciones
        self.timer0 = Timer(0).init(period=100, mode=Timer.ONE_SHOT, callback=self.callback_fin_mediciones)

        # pico de corriente en ambas lineas (l1, l2) en el tiempo de medicion
        pico_corriente_l1 = 0
        pico_corriente_l2 = 0
        # suma de valores de voltaje para promediar
        suma_voltaje = 0
        # index para promediar
        index = 0
        
        while True:
            suma_voltaje += self.voltaje_read()
            index += 1

            # mido sensores de corriente
            try:
                corriente_actual_l1 = self.corriente_dif_read(2, 3)
                corriente_actual_l2 = self.corriente_dif_read(0, 1)
            except:
                pass

            # si la corriente medida es mas alta que el pico previo, sobreescribo
            if corriente_actual_l1 > pico_corriente_l1:
                pico_corriente_l1 = corriente_actual_l1
            # repito en linea 2
            if corriente_actual_l2 > pico_corriente_l2:
                pico_corriente_l2 = corriente_actual_l2

            # si corta el timer
            if self.fin_mediciones:
                # saco promedio de voltaje
                voltaje = suma_voltaje / index
                # saco corriente linea 1 y 2
                corriente_l1 = pico_corriente_l1
                corriente_l2 = pico_corriente_l2
                
                # calculo consumo linea 1 y 2
                consumo_l1 = voltaje * corriente_l1
                consumo_l2 = voltaje * corriente_l2
                
                # guardo en el atributo la medicion
                self.medicion = {"voltaje": int(voltaje), #voltaje de la línea
                                "corriente_l1": round(corriente_l1, 2), #corriente línea 1
                                "corriente_l2": round(corriente_l2, 2), #corriente línea 2
                                "consumo_l1": int(consumo_l1), #consumo línea 1
                                "consumo_l2": int(consumo_l2) #consumo línea 2
                                }
                
                # reinicio variables                
                pico_corriente_l1 = 0
                pico_corriente_l2 = 0
                suma_voltaje = 0
                index = 0
                
                # acumulo voltaje
                self.acumulacion_voltaje_red += voltaje

                # acumulo l1
                if self.l1:
                    self.acumulacion_consumo_l1_solar += consumo_l1
                    self.acumulacion_consumo_solar += consumo_l1
                else:
                    self.acumulacion_consumo_l1_proveedor += consumo_l1
                    self.acumulacion_consumo_red += consumo_l1
                # acumulo l2
                if self.l2:
                    self.acumulacion_consumo_l2_solar += consumo_l2
                    self.acumulacion_consumo_solar += consumo_l2

                else:
                    self.acumulacion_consumo_l2_proveedor += consumo_l2
                    self.acumulacion_consumo_red += consumo_l2
                

                self.indice_mediciones += 1



                # reinicio la variable de callback
                self.fin_mediciones = False
                # rompo el bucle y retorno
                return self.medicion
            
    ################################### CONMUTADOR DE LINEAS #########################################
    
    def conmutador(self, l1, l2):
        self.pedido_conmutacion = True
        self.l1 = l1
        self.l2 = l2
    
    



    
