solarlink-ar/solarlink-web/ESP32_tablero_upython/pruebas_funcionamiento/Medicion consumo + display + comunicacion web/15_5 medicion de consumo con muestreo en display y envio a web/medicion_display_web.py

import machine, time, json, math, ads1115, network
from machine import Pin, ADC, I2C, Timer
from lcd_api import LcdApi
from i2c_lcd import I2cLcd
import urequests as requests
#
#
suma_adc_e = 0
suma_adc_i = 0
index = 0
valores_sens_corriente = []
v_max = 0
timercount = False
#
#
def values_restart():
    global suma_adc_e
    global suma_adc_i
    global index
    global valores_sens_corriente
    global v_max
    suma_adc_e = 0
    suma_adc_i = 0
    index = 0
    valores_sens_corriente = []
    v_max = 0
#
#
def callback_web(tim1): #minute callback
    global timercount
    timercount = True
    print("Timer IRQ")
#
#
tim1 = Timer(1)
tim1.init(period=2000, mode=Timer.PERIODIC, callback=callback_web) #timer init
#
#
wlan = network.WLAN(network.STA_IF) #network init
wlan.active(True)
while not wlan.isconnected():
    try:
        wlan.connect('Red Alumnos', '') #network connection
    except:
        pass
#
#
i2c = I2C(1, scl=Pin(22), sda=Pin(21)) #i2c init
adc_e = ads1115.ADS1115(i2c, 72, 0) #adc externo init

p36 = Pin(36, Pin.IN) #pin init
adc_i = ADC(p36) #adc interno init
adc_i.atten(ADC.ATTN_2_5DB) #atenuacion adc interno
#
#
lcd = I2cLcd(i2c, 0x3f, 2, 16) #inicio lcd
#
#
while 1:
    v_act_sens_i = adc_e.raw_to_v(adc_e.read(7,2,3))
    if v_act_sens_i > v_max:
        v_max = v_act_sens_i
    v_act_sens_v = adc_i.read_uv() / 1000000 * 225 / 1.0193 # mido V del sens. tension de linea rms
    suma_adc_i += v_act_sens_v
    index += 1 # index para el promedio
    
    if timercount:
        lcd.clear()
        sens_corriente = (0.485816226 * pow(v_max,3) -1.1205922* pow(v_max,2) + 5.651277 * v_max) / math.sqrt(2)
        sens_voltaje = int(suma_adc_i/index)
        consumo = sens_voltaje * sens_corriente
        
        lcd.putstr(f'{sens_voltaje} V')
        lcd.move_to(8,0)
        lcd.putstr(f'{round(sens_corriente, 2)} A')
        lcd.move_to(0,1)
        lcd.putstr(f'{round(consumo, 2)} W')
        
        post_data = json.dumps({'sens_voltaje': sens_voltaje, 'sens_corriente': sens_corriente, 'consumo': consumo})
        requests.get('https://helyivan.pythonanywhere.com/datos', data = post_data)
        timercount = False
        values_restart()
    
