solarlink-ar/solarlink-web/ESP32_tablero_upython/tools/display_420_test_tool.py

import machine
from machine import I2C, SoftI2C, Pin
from lcd_api import LcdApi
from i2c_lcd import I2cLcd

I2C_ADDR     = 0x27 #i2c addr
I2C_NUM_ROWS = 4 #filas del lcd
I2C_NUM_COLS = 20 #columnas del lcd

i2c = I2C(1, scl=Pin(26), sda=Pin(27), freq=400000)
#i2c = I2C(1, sda=machine.Pin(21), scl=machine.Pin(22)) #inicio i2c
lcd = I2cLcd(i2c, 0x27, 4, 20) #inicio lcd


lcd.display_on()
lcd.backlight_on()
lcd.hide_cursor()

lcd.clear()
lcd.putstr('Hello world!') #printeo en lcd
